noamkorinperi/VHDL_LAB_final/DOC/Final_report.pdf

## Final project – Report

## MCU and HW-Accelerators architecture and design

## נועם קורין פרי – 208138586

## רועי אגושביץ - 322720665

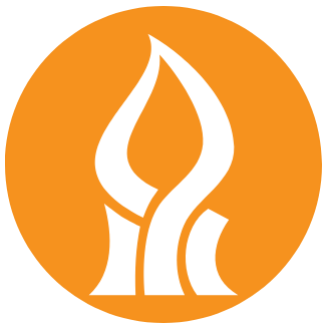
[picture p1: figure]

## תוכן עניינים

.1 הקדמה — עמוד 2
.2 הסבר על המערכת — עמוד 3 .3 תיאור קבצי ה־HDL — עמוד 4 .4 תצוגות RTL של המערכת — עמוד 8 .5 אימות פונקציונלי באמצעות ModelSim — עמוד 12
12 | עמוד | — Test1 – Pushbutton Interrupts and Divider 5.1
13 | עמוד | — Test2 – Basic Timer Periodic Interrupt 5.2
13 | עמוד | — Test3 – Reprogramming the Basic Timer 5.3
14 | עמוד | — Test4 – PWM / Output Compare 5.4
15 | עמוד | — Test4 – Input Capture and Divider 5.5
.6 אימות חומרתי באמצעות SignalTap — עמוד 16
16 | עמוד | — Test1 – KEY1 Interrupt 6.1
17 | עמוד | — Test2 – Basic Timer Interrupt 6.2
17 | עמוד | — Test3 – Basic Timer Interrupt 6.3
18 | עמוד | — Test4 – Integrated Hardware Validation 6.4
18 | עמוד | — Basic Timer Interrupt and CPU Response 6.4.1
18 | עמוד | — KEY1 Interrupt 6.4.2
19 | עמוד | — Divider Accelerator 6.4.3
20 | עמוד | — PWM – Output Compare 6.4.4
.7 אפיון ה־PPA של המערכת — עמוד 22 7.1 Area – ניצול משאבי FPGA — עמוד 22 7.2 Performance – תדר מקסימלי והנתיב הקריטי — עמוד 24 7.3 Power – צריכת הספק — עמוד 27 .8 מסקנות — עמוד 29

## .1 הקדמה

מטרת הפרויקט היא לתכנן ולממש מערכת MCU המבוססת על ליבת IM32RV בארכיטקטורת Cycle-Single, ולשלב סביבה מלאה הכוללת זיכרונות, רכיבי קלט/פלט, פסיקות ומאיץ חומרה. בדומה למעבד ממעבדה ,5 הליבה מבוססת על ארכיטקטורת Harvard ובה זיכרון פקודות ITCM וזיכרון נתונים DTCM, אך בפרויקט זה הורחבה המערכת כך שתתפקד כ־MCU מלא באמצעות O/I Mapped Memory ורכיבים פריפריאליים נוספים.

במסגרת הפרויקט מומשו ממשקי GPIO עבור הלדים, תצוגות ה־-7Segment והמתגים, ממשק ללחצנים 3KEY–1KEY עם תמיכה בפסיקות, Timer Basic הכולל ,Mode Compare
על | האחראי | Interrupt Controller וכן ,Input Captureו־ PWM | ליצירת | Output Compare
זיהוי מקור הפסיקה, קביעת עדיפויות והעברת ערך ה־TYPE למעבד. בנוסף שולב מאיץ חלוקה רב־מחזורי עבור פקודות DIV ו־REM, הפועל בדומיין שעון מהיר יותר ודורש מנגנון סנכרון בין תחומי השעון.

תהליך העבודה כלל כתיבת קוד VHDL ואינטגרציה של כלל רכיבי המערכת, אימות פונקציונלי ב־ModelSim באמצעות אפליקציות ה־Benchmark, אימות על גבי כרטיס ה־FPGA באמצעות SignalTap, ולבסוף אפיון PPA של המערכת ב־Quartus מבחינת שטח, ביצועים וצריכת הספק.

## .2 הסבר על המערכת

המערכת שתוכננה בפרויקט היא MCU המבוסס על ליבת Cycle-Single IM32RV. הליבה מחוברת לשני זיכרונות נפרדים בהתאם לארכיטקטורת Harvard: זיכרון ITCM עבור קוד התוכנית וזיכרון DTCM עבור נתונים. בנוסף לזיכרונות, המעבד מחובר למרחב כתובות של רכיבי O/I Mapped Memory, כך שפקודות load ו־store משמשות גם לגישה לרכיבים הפריפריאליים של המערכת. לפי חלוקת מרחב הכתובות, כתובות הזיכרון הנמוכות משמשות את ה־DTCM, בעוד הכתובות החל מ־2000x0 משמשות את רכיבי הקלט/פלט והבקרה.

רכיבי ה־GPIO כוללים ממשקים ל־LEDR, לתצוגות 5HEX–0HEX ולמתגים SW. עבור רכיבים בעלי יכולת פסיקה נוספו ממשק ללחצנים 3KEY–1KEY, ה־Timer Basic ובקר הפסיקות. ה־Timer Basic כולל רגיסטרי בקרה והשוואה ומאפשר יצירת פסיקות מחזוריות, אות PWM ומדידת זמן באמצעות Capture Input. בקר הפסיקות אוסף את דגלי הפסיקה, בודק אילו מקורות מאופשרים, קובע את המקור בעל העדיפות הגבוהה ביותר ומייצר את ערך ה־TYPE המתאים לפי טבלת וקטורי הפסיקות.

בנוסף לרכיבים הפריפריאליים, משולב במערכת מאיץ חלוקה רב־מחזורי. המאיץ מבצע פעולות חלוקה ושארית במשך 32 מחזורי DIVCLK, בעוד המעבד עצמו פועל על MCLK. בזמן פעולת המאיץ המעבד ממתין לסיום החישוב, ולאחר מכן התוצאה מוחזרת לנתיב ה־Writeback. מכיוון שמדובר בשני תחומי שעון שונים, שולב גם מנגנון CDC לצורך סנכרון האותות ביניהם.

במימוש הסופי נעשה שימוש בשלושה שעונים: MCLK עבור המעבד, SMCLK עבור ה־Timer Basic ו־DIVCLK עבור מאיץ החלוקה. מבנה זה מאפשר להפעיל את המאיץ בתדר גבוה יותר מהליבה, תוך שמירה על פעולה מסודרת של שאר רכיבי ה־MCU.

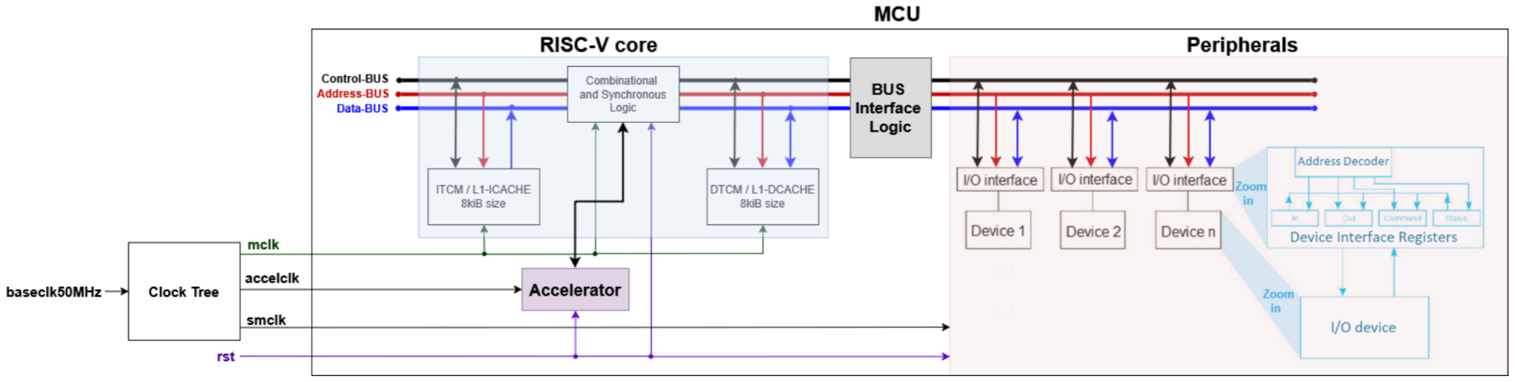
[picture p2: figure]

איור 1 – מבנה ה־Level Top של מערכת ה־MCU based-IM32RV.

## .3 תיאור קבצי ה־HDL

להלן תיאור קצר של קבצי ה־HDL המרכיבים את המימוש הסופי של ה־MCU. קבצי ה־DUT כוללים את ליבת ה־IM32RV, זיכרונות ויחידות הבקרה, רכיבי ה־MMIO, בקר הפסיקות, ה־Timer Basic ומאיץ החלוקה. רשימת הקבצים תואמת למימוש שנמצא .DUT/RV32IMscMCUב־

| קובץ תיאור
Structural בין ליבת המעבד, ה־DTCM, ה־Interconnect, הרכיבים הפריפריאליים ומערכת השעונים, ומחבר את כניסות ויציאות המערכת לכרטיס ה־FPGA. | vhd.IMscMCU32RV קובץ ה־Level Top של המערכת. מחבר באופן
.RV32IM Single-Cycleה־ ליבת של Top Levelה־ קובץ מחבר את יחידות ה־Control ,Decode ,Fetch ו־Execute, וכן את מאיץ ה־Divider ואת מנגנון הטיפול בפסיקות. | RV32I_CORE.vhd

מזיכרון ה־ITCM. בנוסף בוחר את כתובת הפקודה הבאה בהתאם לרצף רגיל, Branch או Jump. | VHD.IFETCH אחראי על ה־Counter Program ועל שליפת הפקודה
מה־File Register, כתיבה חזרה לרגיסטרים ויצירת ערכי ה־Immediate השונים. | VHD.IDECODE מבצע את שלב פענוח הפקודה, כולל קריאת האופרנדים
הפקודה ומייצרת את אותות הבקרה עבור ה־ALU, הזיכרון, Jump/Branch ופקודות ה־Extension M כגון .REMו־ MUL, DIV | VHD.CONTROL יחידת הבקרה הקומבינטורית של המעבד. מפענחת את
חישובי כתובות וזיהוי תנאי Branch. בנוסף משולב בו נתיב הביצוע עבור פעולות הכפל. | VHD.EXECUTE מבצע את הפעולות האריתמטיות והלוגיות של ה־ALU,
והכתיבה של המעבד. | VHD.DMEMORY מממש את זיכרון הנתונים DTCM, כולל פעולות הקריאה
הכפלת שני האופרנדים והפקת תוצאת הכפל לנתיב הביצוע. | vhd16.Multiplier מממש את יחידת הכפל של פקודת MUL, המבוססת על
המערכת משעון ה־50 MHz של הכרטיס. במימוש הסופי | vhd.PLL מממש את ה־PLL המשמש להפקת שעון העבודה של

ליבת המעבד פועלת ב־20 MHz, בעוד מאיץ החלוקה משתמש ב־50 MHz.

הטיימר תומך ב־Mode Compare ליצירת פסיקות Inputו־ PWM ליצירת Output Compare , מחזוריות Capture לשמירת ערך המונה בעת אירוע חיצוני. | vhd.timer_basic מממש את ה־Timer Basic ואת רגיסטרי הבקרה שלו.
רגיסטרי IE ו־IFG, קובע את מקור הפסיקה בעל העדיפות הגבוהה ביותר, מפיק את ערך ה־TYPE ומייצר את אות INTR למעבד. | vhd.controller_interrupt מממש את בקר הפסיקות של המערכת. שומר את
מצב הלחצנים ומייצר אירוע פסיקה בעת שחרור לחצן, בהתאם למעבר מ־0 ל־1 של אות ה־KEY. | vhd.unit_pushbutton מממש את ממשק 3KEY–1KEY. מאפשר קריאה של
תצוגות 5HEX–0HEX והמתגים SW, כולל קריאה וכתיבה לפי כתובות ה־MMIO. | vhd.peripheral_gpio מממש את רכיבי ה־GPIO הממופים לזיכרון: LEDR,
ומחבר ביניהם לבין ממשק ה־MMIO. כולל את ה־GPIO, הלחצנים, ה־Timer Basic ובקר הפסיקות. | vhd.peripherals_mcu מרכז את כלל הרכיבים הפריפריאליים של ה־MCU
שמפיק המעבד ומנתב כל פעולת Store/Load אל | vhd.interconnect_mcu מממש את לוגיקת ה־Interface Bus. בודק את הכתובת

ה־DTCM או אל מרחב ה־MMIO, ומחזיר למעבד את הנתונים מהיעד המתאים.

מכיל את קבועי מפת הזיכרון של ה־MCU, ובהם תחומי ה־DTCM וה־MMIO והכתובות של רכיבי ה־GPIO, הטיימר ובקר הפסיקות. | mcu_memory_map_pkg.vh d
החלוקה מתבצעת באלגוריתם רב־מחזורי במשך 32 מחזורי שעון ומפיקה מנה ושארית. | vhd.unsigned_divider מממש את ליבת המחלק הבלתי־מסומן. פעולת
מטפל בפקודות REM/DIV, באותות done/busy ובמעבר בין תחום שעון ה־MCLK לתחום ה־DIVCLK באמצעות מנגנון CDC. | vhd.accelerator_divider עוטף את המחלק ומחבר אותו לליבת המעבד. הקובץ
מסכות לפענוח פקודות וקבועים המשמשים את יחידות ה־Control וה־Datapath. | vhd.package_const מכיל קבועים משותפים לליבת המעבד, כגון Opcodes,
מכיל פרמטרים גלובליים של התכן, כגון גדלי הזיכרונות ורוחבי הכתובות, ומשמש להגדרת תצורת הקומפילציה של המערכת. | cond_compilation_package .vhd
משותפות Genericsו־ Components הצהרות מכיל המשמשות לחיבור מבני של יחידות המעבד והמערכת. | aux_package.vhd

## .4 תצוגות RTL של המערכת

לאחר השלמת הסינתזה ב־Quartus נבדק מבנה המערכת באמצעות ה־Viewer RTL. מטרת הבדיקה היא לוודא שהמודולים המרכזיים של המערכת חוברו כפי שתוכנן, ולראות את ההיררכיה והקשרים בין ליבת המעבד, הזיכרונות, הרכיבים הפריפריאליים ומאיץ החלוקה. דרישה להצגת תוצאות ה־Viewer RTL מופיעה במפורש בסעיף 10 של הוראות הפרויקט.

בתצוגת ה־Level Top ניתן לראות את ליבת ה־Cycle-Single IM32RV מחוברת ל־ITCM ול־DTCM, את ממשק ה־MMIO המחבר את המעבד לרכיבי ה־GPIO ולרכיבים בעלי יכולת פסיקה, וכן את מערכת השעונים והחיבור למאיץ החלוקה. המבנה משקף את ארכיטקטורת ה־MCU הכללית שנדרשה בפרויקט.

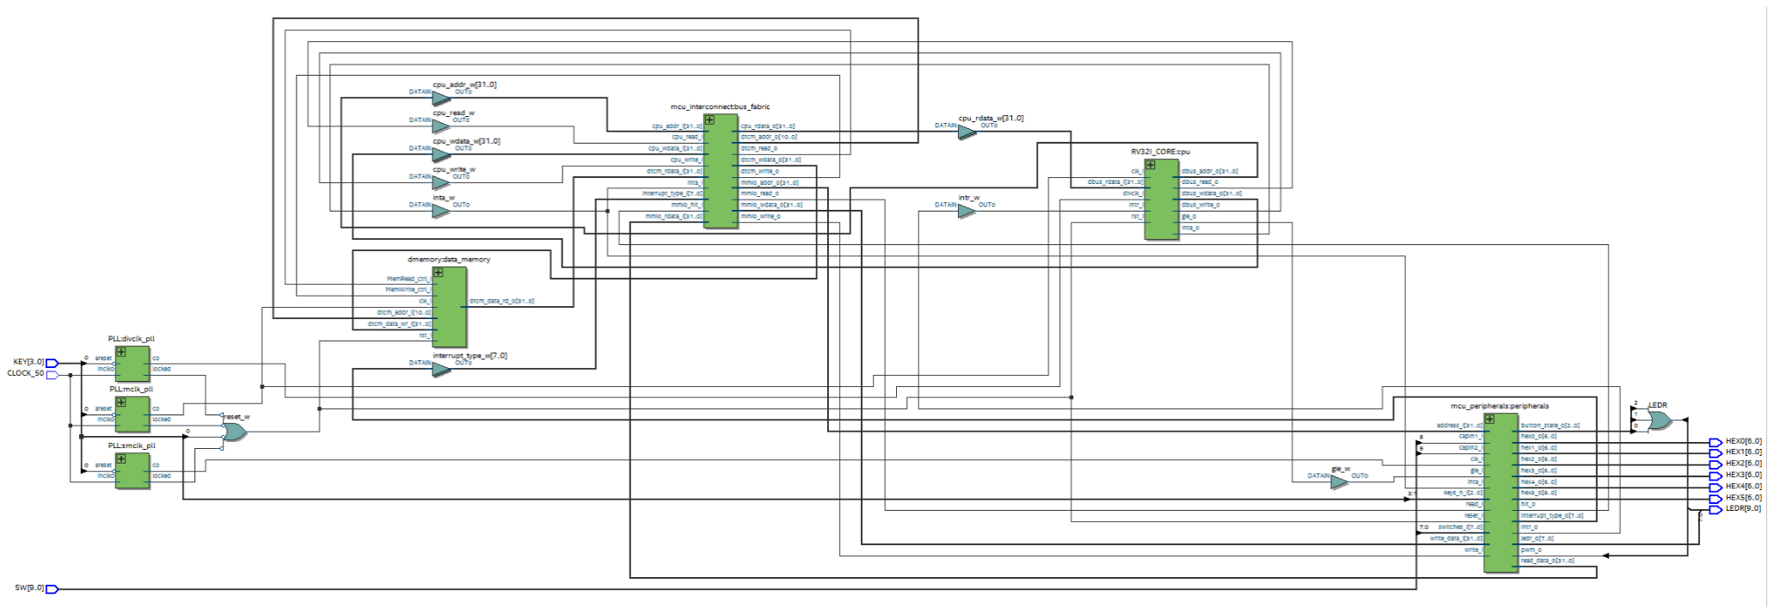
[picture p3: figure]

איור 2 - תצוגת RTL של ה־Level Top של מערכת ה־MCU based-IM32RV.

בנוסף נבדקה תצוגת ה־RTL של ליבת המעבד ושל נתיב מאיץ החלוקה. ניתן לראות את יחידות ה־Control ,Decode ,Fetch ו־Execute של הליבה החד־מחזורית, וכן את החיבור בין האופרנדים של המעבד למאיץ ה־Divider ואת החזרת תוצאת ה־Quotient או ה־Remainder לנתיב ה־Writeback. מבנה זה תואם לארכיטקטורה הנדרשת של ליבת IM32RV עם מאיץ חלוקה רב־מחזורי.

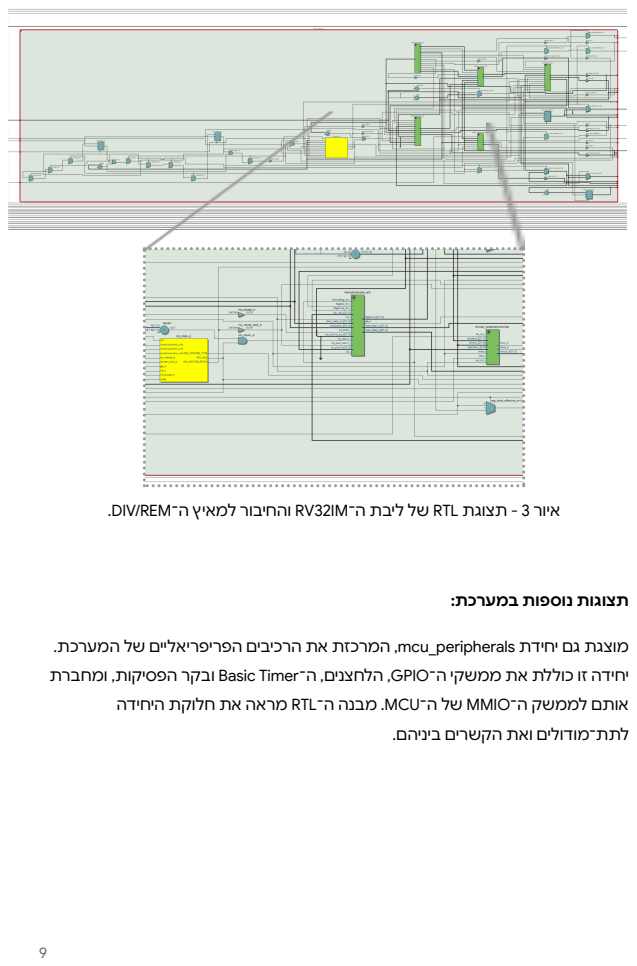
[picture p4: page 10]

איור 3 - תצוגת RTL של ליבת ה־IM32RV והחיבור למאיץ ה־REM/DIV.

תצוגות נוספות במערכת:

מוצגת גם יחידת peripherals_mcu, המרכזת את הרכיבים הפריפריאליים של המערכת.
יחידה זו כוללת את ממשקי ה־GPIO, הלחצנים, ה־Timer Basic ובקר הפסיקות, ומחברת

אותם לממשק ה־MMIO של ה־MCU. מבנה ה־RTL מראה את חלוקת היחידה

לתת־מודולים ואת הקשרים ביניהם.

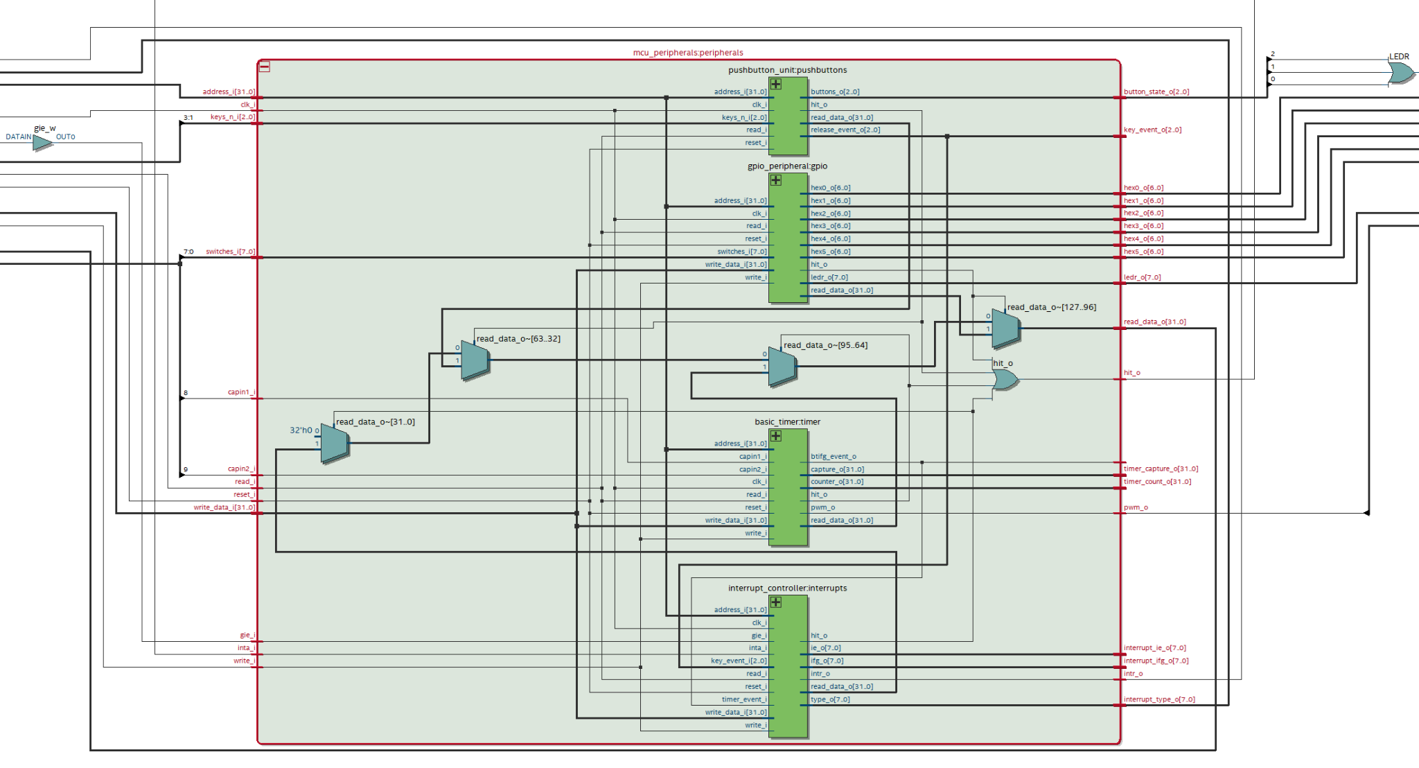
[picture p5: figure]

איור 4 – תצוגת RTL של מערך הרכיבים הפריפריאליים של ה־MCU.

בהמשך נבחן גם ה־Controller Interrupt, שהוא אחד הרכיבים המרכזיים שנוספו למערכת לצורך תמיכה בפסיקות. ניתן לזהות בו את הלוגיקה הקשורה לרגיסטרי IFG ,IE ו־TYPE, וכן את החיבור למקורות הפסיקה השונים. הבקר אחראי לסינון הפסיקות לפי ביטי ה־Enable, לקביעת מקור הפסיקה בעל העדיפות הגבוהה ביותר ולהעברת בקשת הפסיקה וה־TYPE המתאים אל המעבד.

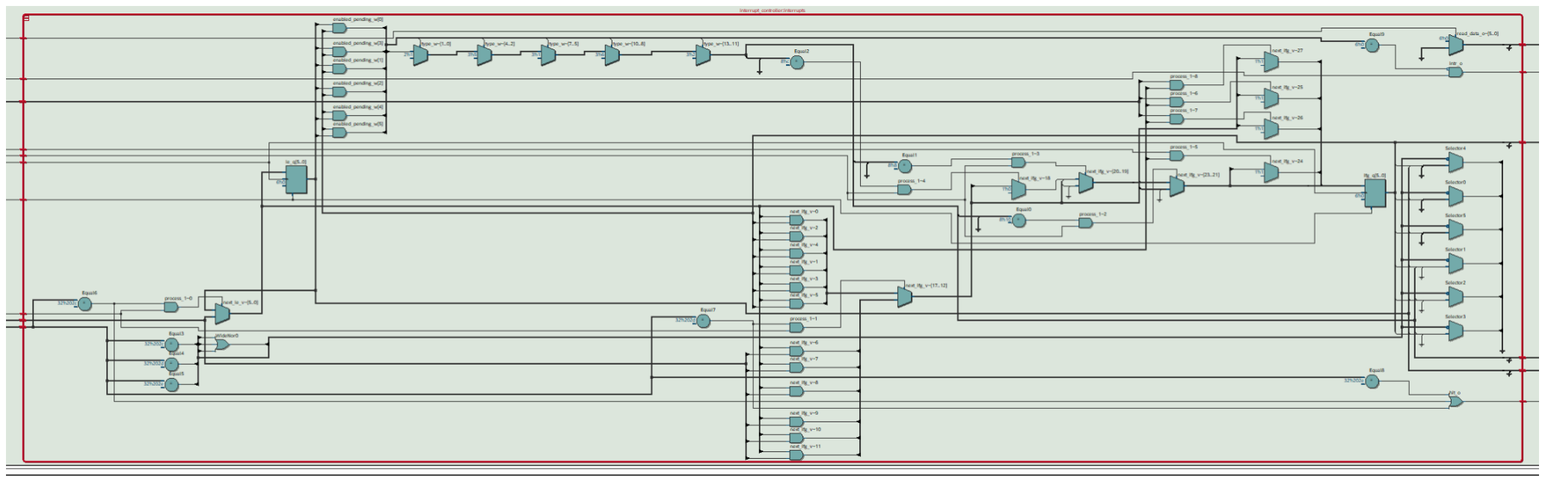
[picture p6: figure]

איור 5 – תצוגת RTL של בקר הפסיקות.

לבסוף נציג גם את מערכת השעונים של ה־MCU. המערכת משתמשת בשלושה אותות שעון נפרדים המופקים מ־50_CLOCK: MCLK עבור ליבת המעבד, SMCLK עבור ה־Basic Timer ו־DIVCLK עבור מאיץ החלוקה. במימוש הסופי MCLK ו־SMCLK פועלים בתדר 20 MHz, בעוד DIVCLK פועל בתדר 50 MHz.

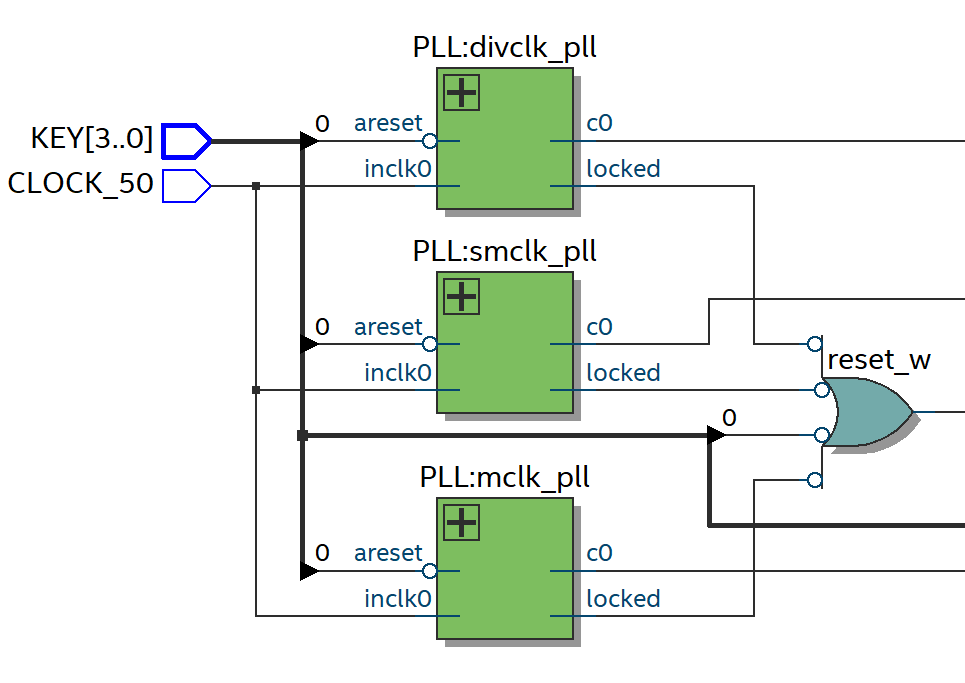
[picture p7: figure]

איור 6 – תצוגת RTL של מערכת השעונים וה־PLL של ה־MCU.

## .5 אימות פונקציונלי באמצעות ModelSim

לאחר השלמת האינטגרציה של רכיבי ה־MCU בוצע אימות פונקציונלי ב־ModelSim באמצעות ארבע אפליקציות ה־Benchmark שניתנו לפרויקט. מטרת הסימולציות הייתה לבדוק לא רק את פעולת כל רכיב בנפרד, אלא גם את שיתוף הפעולה בין ליבת המעבד, ה־O/I Mapped Memory, בקר הפסיקות, ה־Timer Basic ומאיץ החלוקה. במהלך ההרצות נבדקו אותות ה־MMIO, דגלי הפסיקה, אותות INTR ו־INTA, פעילות ה־Divider וכן רגיסטרי ה־Timer Basic.

Test1 – Pushbutton Interrupts and Divider 5.1

ב־1Test נבדקה תגובת המערכת לפסיקות הנוצרות מהלחצנים 3KEY–1KEY. לחיצות 1KEY ו־2KEY משמשות להצגת איברים מהמערכים על תצוגות ה־HEX, ואילו 3KEY מפעיל פעולות DIV ו־REM באמצעות מאיץ החלוקה. בתרשים הגלים ניתן לעקוב אחר שרשרת הטיפול בפסיקה החל משינוי מצב ה־KEY, דרך יצירת דגל ה־IFG והעלאת INTR, ועד לאישור הפסיקה על ידי המעבד באמצעות INTA. בהמשך ניתן לראות גם את פעילות מאיץ ה־Divider ואת החזרת תוצאת החישוב למעבד. לדוגמה, עבור האופרנדים הראשונים 100=1arr ו־8=2arr מתקבלים מנה 12 ושארית ,4 בהתאם לתוצאה הצפויה.

המטרה של הבדיקה היא להראות שמסלול הפסיקה מהלחצן אל המעבד פועל כראוי, ושלאחר הטיפול בפסיקה המעבד מסוגל להפעיל את מאיץ החלוקה ולקבל ממנו תוצאה תקינה.

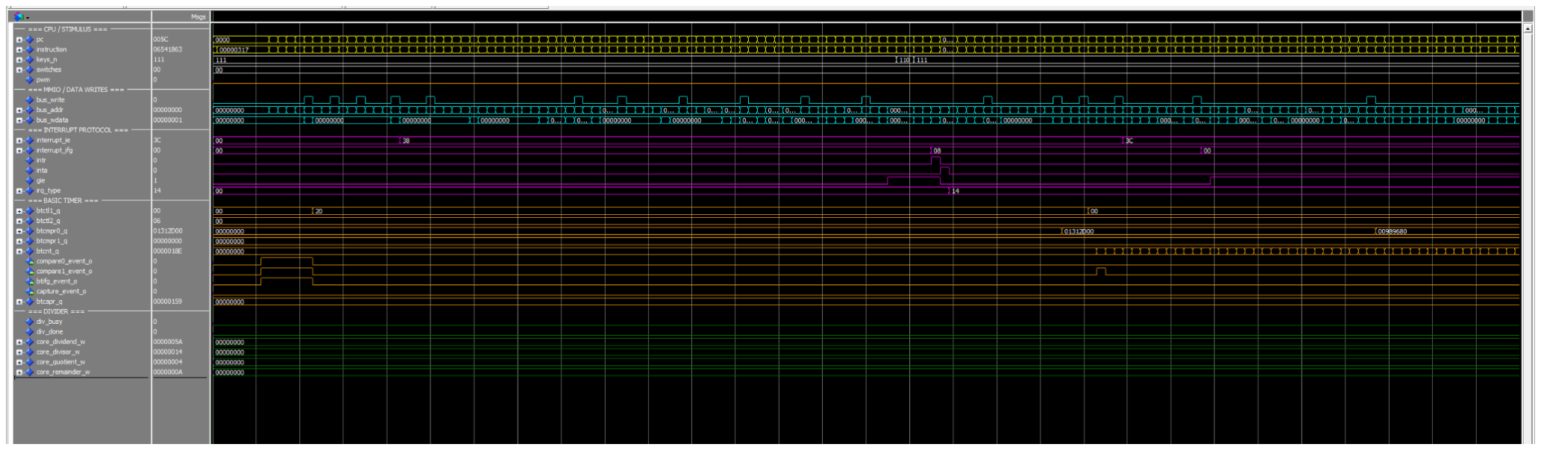
[picture p8: figure]

איור 7 – סימולציית ModelSim של 1Test – פסיקות לחצנים ופעולת מאיץ ה־Divider.

Test2 – Basic Timer Periodic Interrupt 5.2

ב־2Test נבדקה פעולת ה־Timer Basic כמקור לפסיקה מחזורית. בכל אירוע Timer נוצר BTIFG, בקר הפסיקות מזהה את מקור הפסיקה ומעביר למעבד 10x0=TYPE, בהתאם לטבלת וקטורי הפסיקות. לאחר מכן המעבד מאשר את הפסיקה באמצעות INTA ונכנס לשגרת הטיפול המתאימה.

שגרת הפסיקה מגדילה את הרגיסטר 0a, כאשר 3KEY–1KEY קובעים באיזה זוג תצוגות HEX יוצג הערך. בתרשים הגלים ניתן לראות את אירוע הטיימר, עדכון ה־IFG, יצירת INTR, אישור הפסיקה ולבסוף את עדכון הערך. לאחר הפסיקה הראשונה מתקבל 1=0a, כפי שנדרש באפליקציית ה־Benchmark. בדיקה זו מאמתת את שרשרת הטיפול המלאה בפסיקה פנימית של ה־MCU, החל מה־Timer Basic ועד לביצוע שגרת הפסיקה על ידי המעבד.

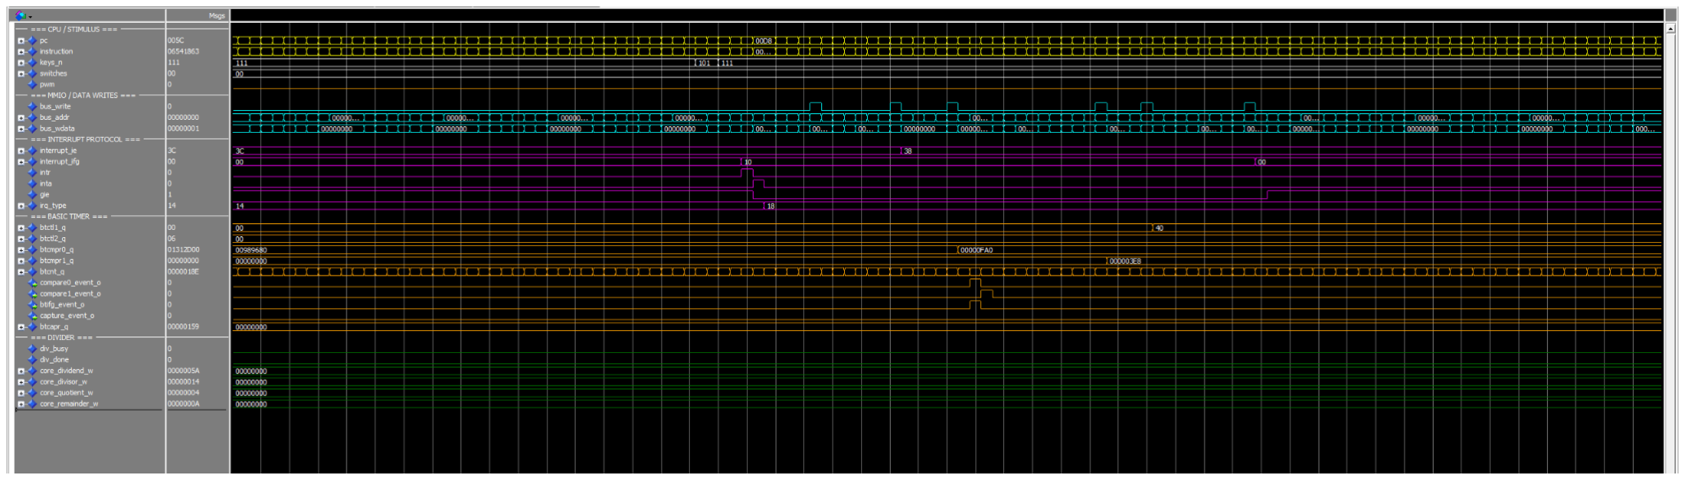
[picture p9: figure]

איור 8 – סימולציית ModelSim של 2Test – פסיקה מחזורית של ה־Timer Basic.

Test3 – Reprogramming the Basic Timer 5.3

ב־3Test נבדקה האפשרות לשנות בזמן ריצה את תקופת הפסיקות של ה־Timer Basic. לחיצות על 2KEY 1,KEY ו־3KEY גורמות לכתיבת ערכים חדשים ל־0BTCMPR, המתאימים לתקופות של /2PERIOD_SEC, /4PERIOD_SEC ו־/8PERIOD_SEC. בתרשים הגלים ניתן לראות את כתיבות ה־MMIO לרגיסטר ההשוואה ואת השינוי בהתנהגות הטיימר לאחר התכנות מחדש. בנוסף נבדקה פעולת מנגנון ה־buffering double של רגיסטר ההשוואה: הערך החדש נכתב ל־0BTCMPR ומועבר ל־Latch המשמש בפועל להשוואה מול BTCNT,

כך ששינוי ערך ההשוואה מתבצע בצורה מבוקרת. מנגנון זה תואם למבנה ה־Timer Basic שהוגדר בפרויקט.

הבדיקה מראה כי תוכנת ה־Benchmark מסוגלת לשנות את תקופת הטיימר בזמן ריצה באמצעות כתיבות MMIO, וכי הפסיקות הבאות מתקבלות בהתאם לערך ההשוואה החדש.

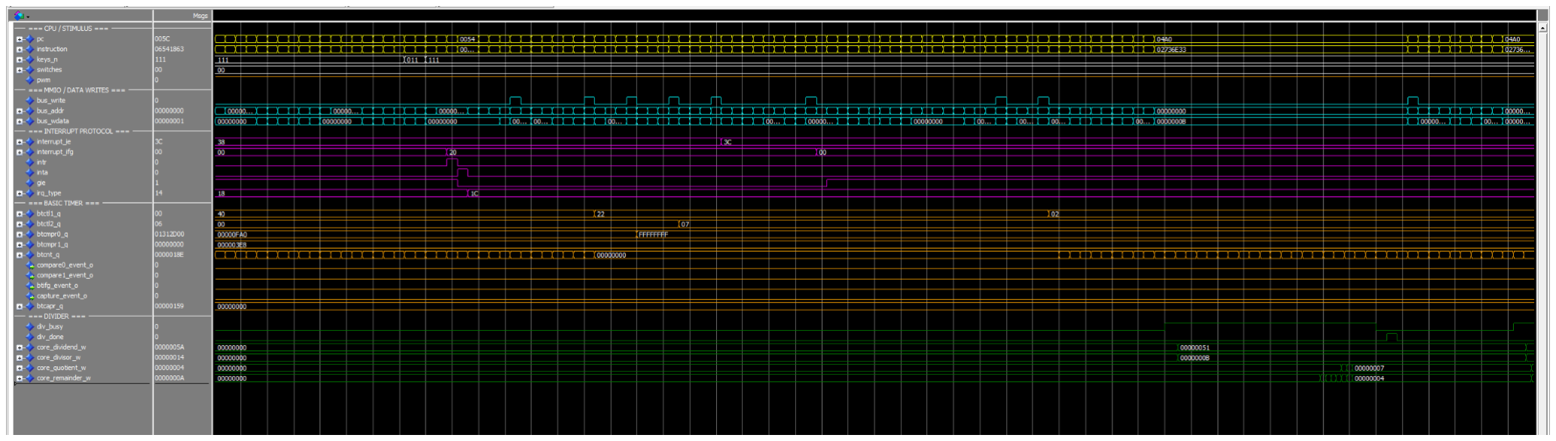
[picture p10: figure]

איור 9 – סימולציית ModelSim של 3Test – תכנות מחדש של תקופת ה־Timer Basic.

Test4 – PWM / Output Compare 5.4

החלק הראשון של 4Test בודק את מצב ה־Compare Output של ה־Timer Basic ואת יצירת אות ה־PWM. לאחר לחיצה על 2KEY מבוצעות כתיבות MMIO לרגיסטרי הטיימר, ובפרט ל־0BTCMPR ול־1BTCMPR.

0BTCMPR קובע את תקופת ה־PWM ונשאר בערך 0FA00000x0( 4000 מחזורי SMCLK), בעוד 1BTCMPR קובע את נקודת ההשוואה בתוך המחזור. ה־Benchmark משנה את ערך 1BTCMPR כך שמתקבלים Cycles Duty של ,50% ,75% 87.5% ו־.93.75% בתרשים ModelSim ניתן לראות את כתיבות ה־MMIO ואת שינוי ערכי רגיסטרי ההשוואה; ההתנהגות הפיזית של אות ה־PWM עצמו נבדקת בהמשך באמצעות SignalTap.

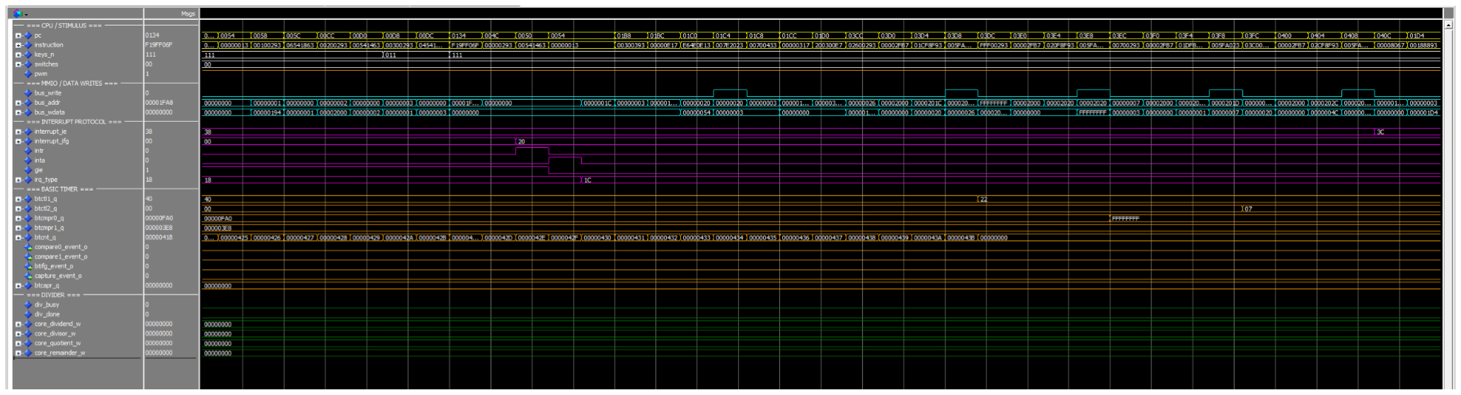
[picture p11: figure]

איור 10 – סימולציית ModelSim של 4Test – תכנות ה־Timer Basic במצב Output .Compare / PWM

Test4 – Input Capture and Divider 5.5

בחלק נוסף של 4Test נבדק מצב ה־Capture Input של ה־Timer Basic, המשמש למדידת זמן הריצה של פעולות DIV ו־REM. מאיץ החלוקה פועל במשך מספר מחזורי DIVCLK, ובסיום הפעולה מופק אירוע המשמש ללכידת ערך BTCNT לתוך BTCAPR.

בתרשים ניתן לראות את אותות ה־done/busy של מאיץ החלוקה, את האופרנדים והתוצאות, ובמקביל את אירוע ה־Capture ואת עדכון BTCAPR. אפליקציית ה־Benchmark מבצעת סדרת פעולות REM ולאחר מכן DIV, וה־Testbench מאמת שתוצאות המערכים נשמרו ושערכי זמן הריצה שנלכדו אינם אפס. בדיקה זו מאמתת את העבודה המשותפת בין שלושה חלקים מרכזיים במערכת: ליבת המעבד, מאיץ ה־Divider .Basic Timerוה־

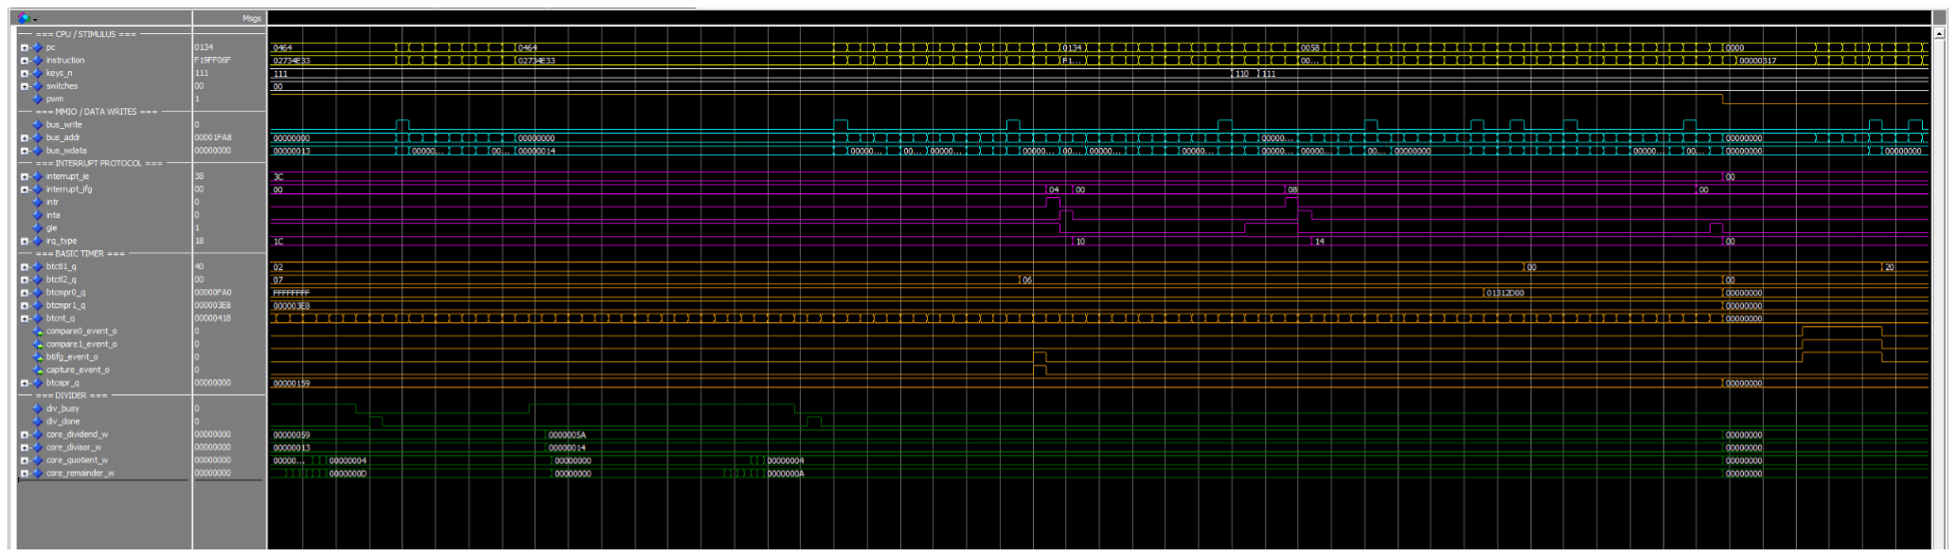
[picture p12: figure]

איור 11 – סימולציית ModelSim של Capture Input – 4Test ומדידת פעולת ה־Divider.

ארבע בדיקות ה־Benchmark מאפשרות לבדוק את המערכת ברמת אינטגרציה מלאה ולא רק ברמת יחידות בודדות. הסימולציות מאמתות את פעולת ה־GPIO והלחצנים,
,Input Captureו־ Compare, Output Compare | במצבי | Basic Timerה־ , | הפסיקות | מנגנון
וכן את פעולת מאיץ ה־REM/DIV והתקשורת שלו עם ליבת המעבד.

## .6 אימות חומרתי באמצעות SignalTap

לאחר השלמת האימות הפונקציונלי ב־ModelSim, בוצע אימות של המערכת על גבי כרטיס ה־FPGA באמצעות SignalTap. מטרת הבדיקה הייתה לוודא שהתנהגות המערכת שנצפתה בסימולציה מתקיימת גם במימוש הפיזי לאחר סינתזה ו־Route & Place. במהלך הרצת אפליקציות ה־Benchmark נלכדו אותות פנימיים מרכזיים, ובהם רגיסטר ה־IFG,
רגיסטרי | ,PCה־ | רצף ,irq_vector_load_wו־ irq_accept_w ,INTA | אותות | ,TYPEה־ | ערך
ה־Timer Basic ואותות מאיץ החלוקה.

Test1 – KEY1 Interrupt 6.1

במהלך הרצת 1Test נלכד ב־SignalTap תהליך הטיפול בפסיקת 1KEY. באיור 12 ניתן לראות כי רגיסטר ה־IFG מקבל את הערך h,08 המתאים ל־IFG1KEY, ובמקביל w_type_interrupt מקבל את הערך h,14 בהתאם לטבלת וקטורי הפסיקות. לאחר מכן הערך h14 נלכד ב־q_type_irq.

ובמקביל | ,irq_vector_load_wו־ INTA ,irq_accept_w | מופעלים | הלכידה | בהמשך
משתנה רצף ה־PC. בכך מאומת בחומרה מסלול הטיפול בפסיקת 1KEY, החל מזיהוי מקור הפסיקה ועד להעברת המעבד לשגרת הפסיקה.

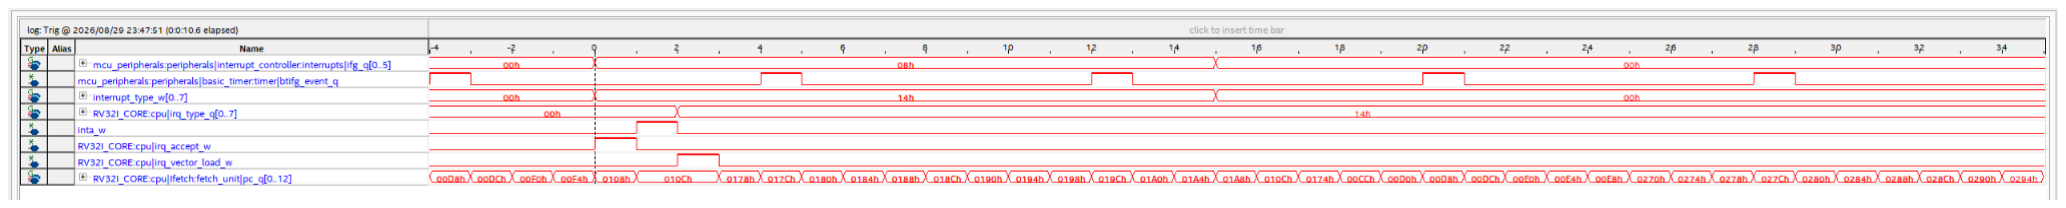
[picture p13: figure]

איור 12 – אימות SignalTap של 1Test – טיפול בפסיקת 1KEY.

Test2 – Basic Timer Interrupt 6.2

ב־2Test נלכדה פסיקה שמקורה ב־Timer Basic. באיור 13 ניתן לראות את עליית q_event_btifg, ולאחריה רגיסטר ה־IFG מקבל את הערך h,04 המתאים ל־BTIFG. במקביל בקר הפסיקות מפיק h10=TYPE, והערך נלכד ב־q_type_irq.

ורצף | ,irq_vector_load_wו־ INTA ,irq_accept_w | מופעלים | הפסיקה | זיהוי | לאחר
ה־PC משתנה בהתאם לכניסה לשגרת הטיפול בפסיקה. הלכידה מאמתת את שרשרת הטיפול המלאה בפסיקת Timer Basic על גבי ה־FPGA.

איור 13 – אימות SignalTap של 2Test – טיפול בפסיקת Timer Basic.

Test3 – Basic Timer Interrupt 6.3

במהלך 3Test נלכדה שוב פסיקה שמקורה ב־Timer Basic. באיור 14 ניתן לראות את q_event_btifg, את עדכון ה־IFG ל־h04 ואת יצירת h10=TYPE. לאחר מכן מופעלים
עובר | PCוה־ ,irq_vector_load_wו־ INTA ,irq_accept_w | בפסיקה | הטיפול | אותות
לרצף המתאים לשגרת הפסיקה.

לכידה זו מאמתת כי גם במהלך 3Test מנגנון הפסיקות של ה־Timer Basic ממשיך לפעול באופן תקין לאחר תכנות הטיימר על ידי התוכנה.

איור 14 – אימות SignalTap של 3Test – טיפול בפסיקת Timer Basic.

Test4 – Integrated Hardware Validation 6.4

ב־4Test בוצע אימות חומרתי מפורט יותר של מספר מנגנונים במערכת: פסיקת Basic Timer ותגובת המעבד, פסיקת 1KEY, פעולת מאיץ החלוקה ויצירת אות PWM באמצעות .Output Compare

Basic Timer Interrupt and CPU Response 6.4.1

באיור 15 ניתן לראות את BTCNT מתקדם עד לערך ההשוואה 00989680x0=0BTCMPR. עם הגעת המונה לערך ההשוואה נוצר אירוע q_event_btifg, רגיסטר ה־IFG מתעדכן ל־h04 ובקר הפסיקות מפיק h10=TYPE. לאחר מכן הערך h10 נלכד ב־q_type_irq,
.irq_vector_load_wו־ INTA ,irq_accept_w | ומופעלים

באותה לכידה ניתן לראות גם את שינוי רצף ה־PC ואת חזרת BTCNT לערך אפס לאחר אירוע ההשוואה. בכך מאומת בחומרה הקשר המלא בין פעולת הטיימר לבין מנגנון הפסיקות ותגובת ה־CPU.

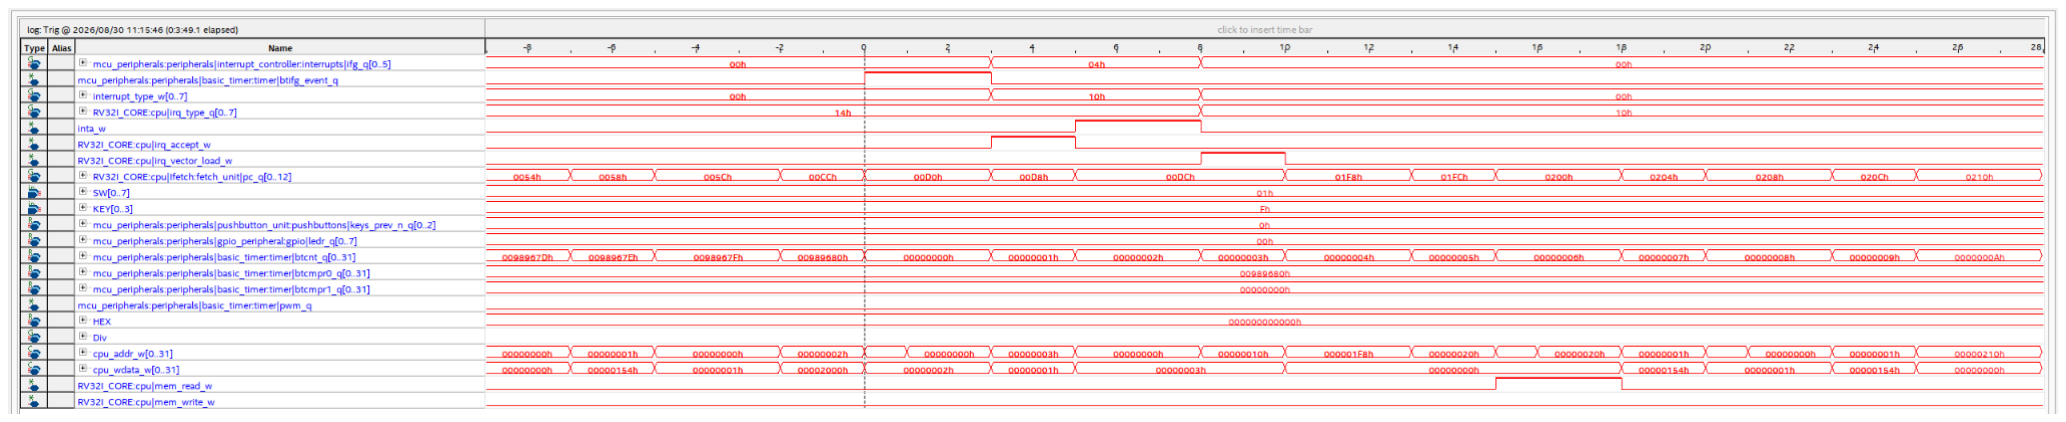
[picture p14: figure]

איור 15 – אימות SignalTap של 4Test – פסיקת Timer Basic ותגובת ה־CPU.

KEY1 Interrupt 6.4.2

באיור 16 מוצגת פסיקת 1KEY במהלך 4Test. ניתן לראות את אוטובוס 3:0]KEY ]משתנה מ־Dh ל־Fh, כלומר 1KEY עובר ממצב לחוץ למצב משוחרר. לאחר האירוע רגיסטר ה־IFG מקבל את הערך h,08 ו־w_type_interrupt מקבל h.14

INTA ,irq_accept_w | ומופעלים | ,irq_type_qב־ | נלכד | TYPE=14h | בהמשך
ו־w_load_vector_irq. במקביל משתנה ה־PC לשגרת הפסיקה. הלכידה מאמתת בחומרה את זיהוי אירוע 1KEY ואת הטיפול בו על ידי בקר הפסיקות והמעבד.

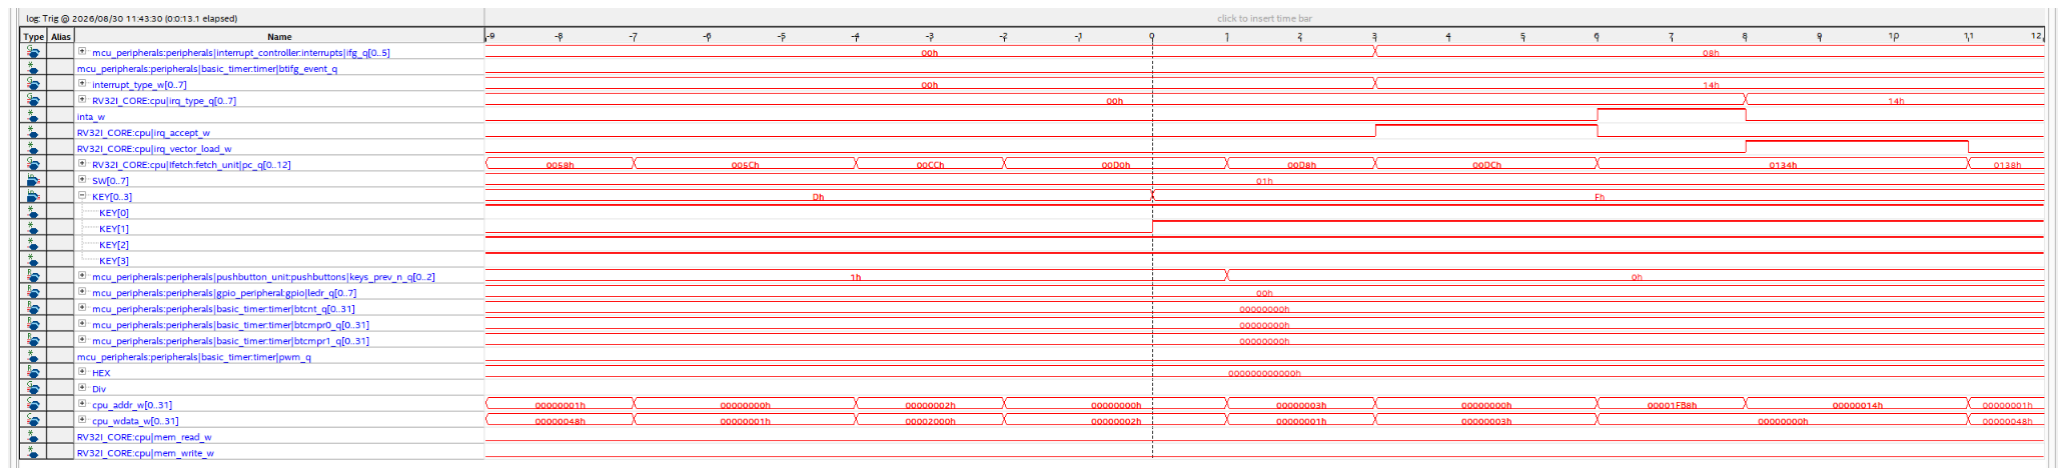
[picture p15: figure]

איור 16 – אימות SignalTap של 4Test – פסיקת 1KEY.

Divider Accelerator 6.4.3

באיור 17 מוצגת פעולת מאיץ החלוקה במהלך 4Test. ניתן לראות את התקדמות q_count עד Fh,1 ובמקביל את השינוי ההדרגתי ברגיסטרים הפנימיים של אלגוריתם החלוקה. האופרנד q_divisor שווה ל־,8 ובסיום הפעולה מתקבלים 7=q_quotient .remainder_q=4ו־

בסיום החישוב מופעל q_done, ולאחר מכן מתקבל גם w_done_div בצד המעבד. הלכידה מאמתת הן את פעולת האלגוריתם הרב־מחזורי לאורך מחזורי DIVCLK והן את העברת סימון סיום החישוב והתוצאה חזרה לליבת המעבד.

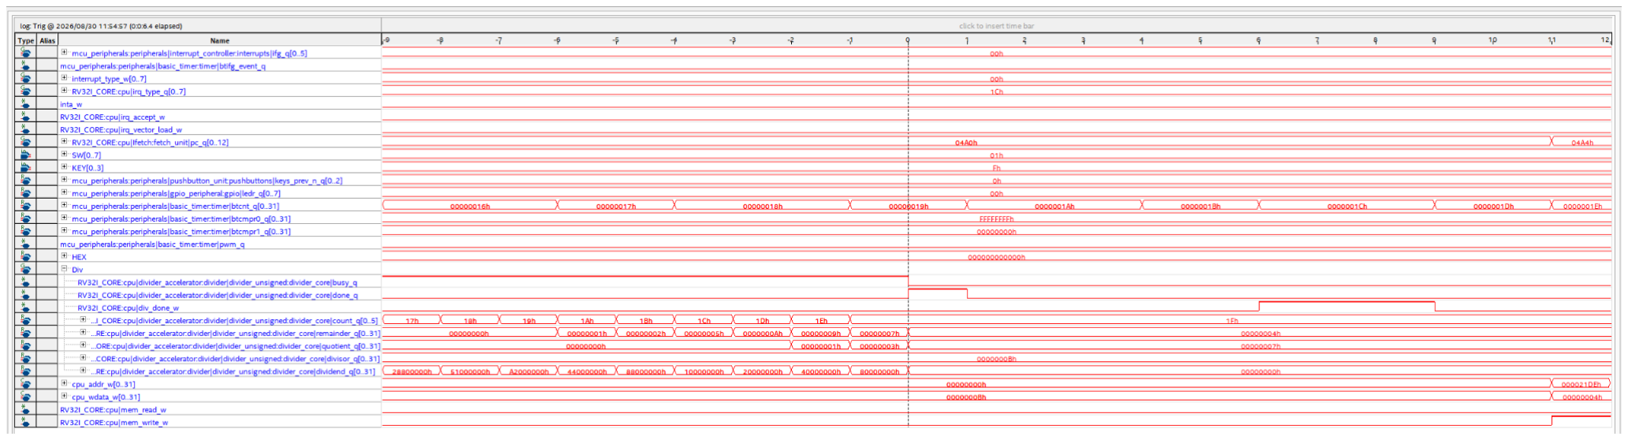
[picture p16: figure]

איור 17 – אימות SignalTap של 4Test – פעולת מאיץ ה־Divider.

PWM – Output Compare 6.4.4

בחלק האחרון של 4Test נבדקה פעולת ה־PWM של ה־Timer Basic. בכל ארבע הלכידות 0BTCMPR נשאר קבוע בערך 0FA00000x,0 כלומר 4000 מחזורי SMCLK, בעוד 1BTCMPR משתנה וקובע את נקודת ה־Compare Output.

באיורים 18–21 מתקבלים הערכים:

עבור | 0x00000DAC ,75% | עבור | 0x00000BB8 ,50% | עבור | BTCMPR1=0x000007D0
87.5% ו־6EA00000x0 עבור .93.75% ערכים אלו הם בהתאמה ,2000 ,3000 3500 ו־3750 מתוך תקופה של 4000 ספירות. במקביל מוצג האות pwm_q, ונקודת שינוי המצב שלו משתנה בהתאם לערך ההשוואה שנבחר.

כך מאומת כי שינוי 1BTCMPR באמצעות 4Test משנה בפועל את ה־Cycle Duty של אות ה־PWM, בעוד תקופת ה־PWM נשארת קבועה. עבור MHz 20=SMCLK ותקופה של 4000 מחזורים מתקבל תדר PWM של 5 kHz.

PWM Duty Cycle variation using KEY2

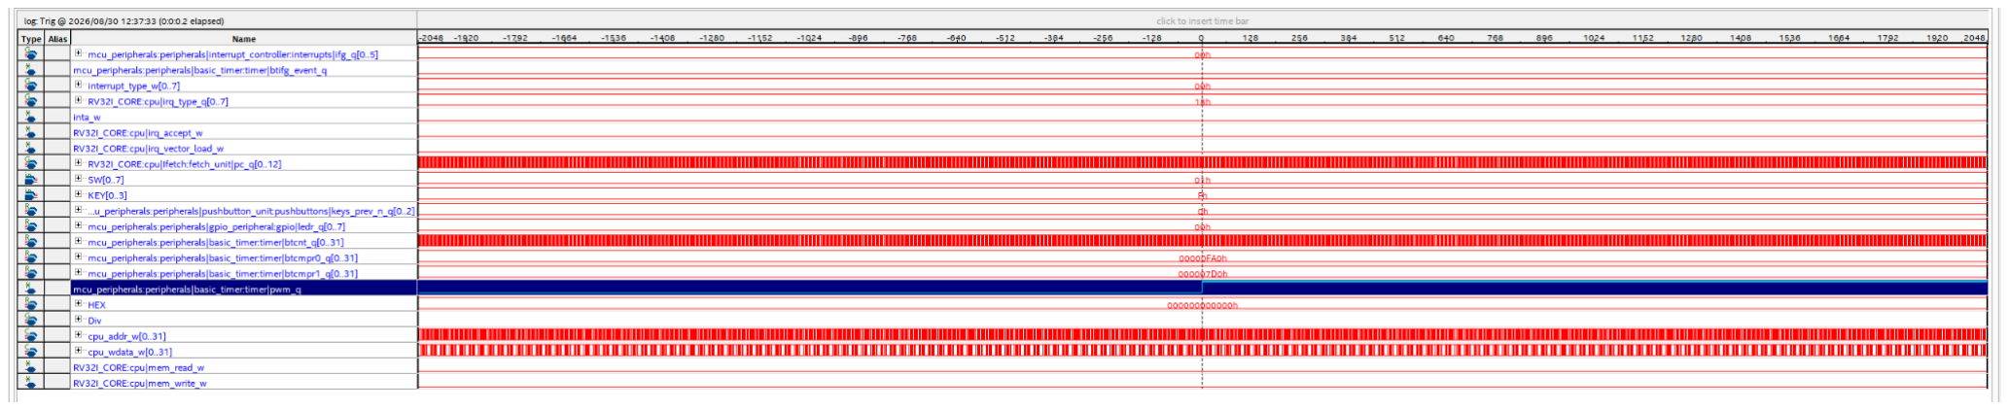
[picture p17: figure]

.BTCMPR1=0x000007D0 ,50% של Duty Cycleב־ PWM של SignalTap | אימות | – 18 איור

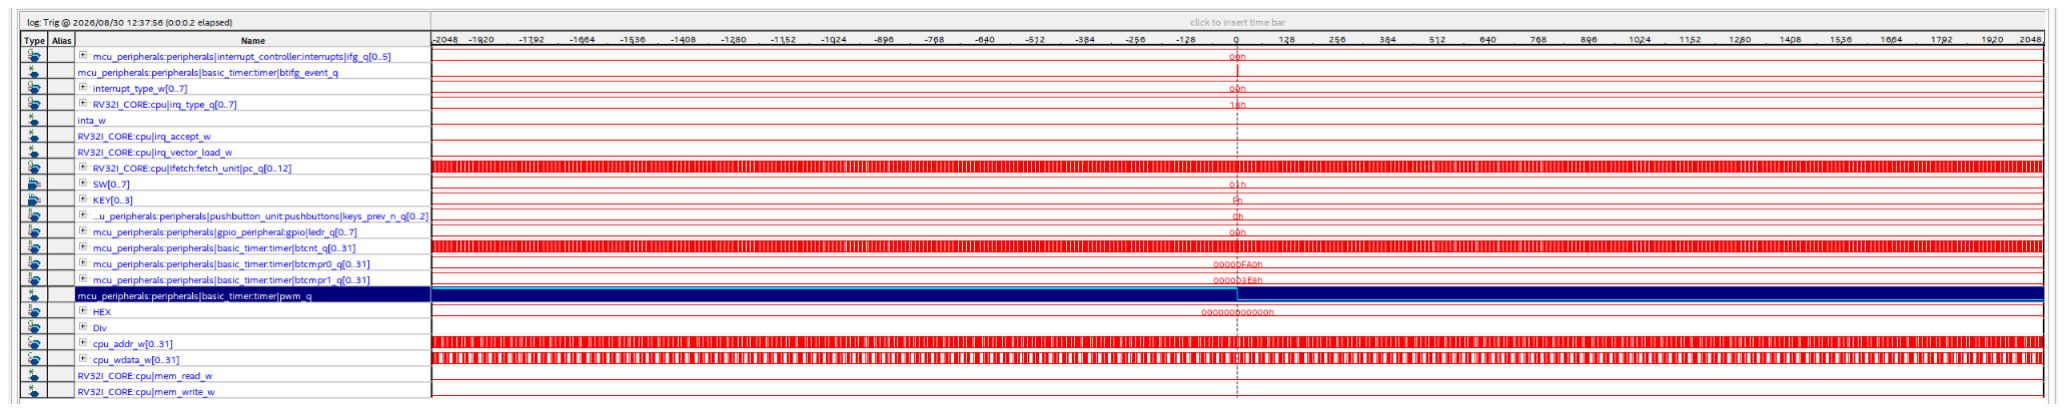
[picture p18: figure]

.BTCMPR1=0x00000BB8 ,75% של Duty Cycleב־ PWM של SignalTap | אימות | – 19 איור

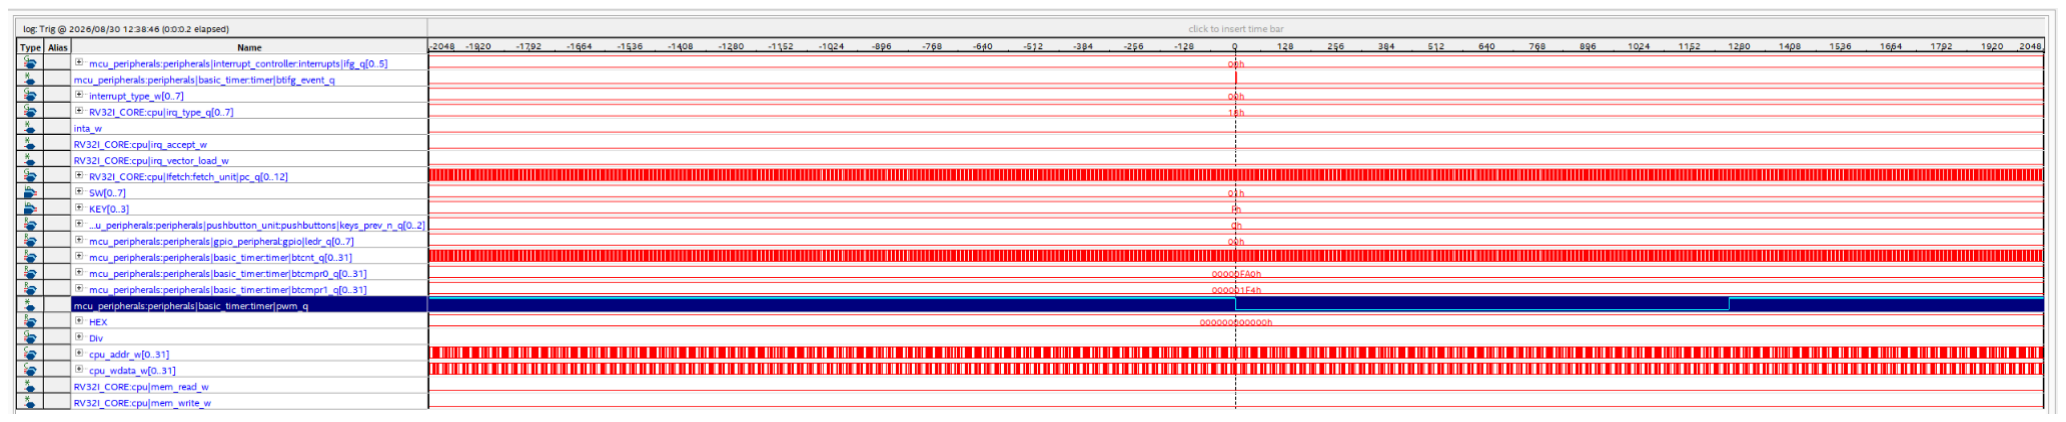
[picture p19: figure]

איור 20 – אימות SignalTap של PWM ב־Cycle Duty של ,87.5% .BTCMPR1=0x00000DAC

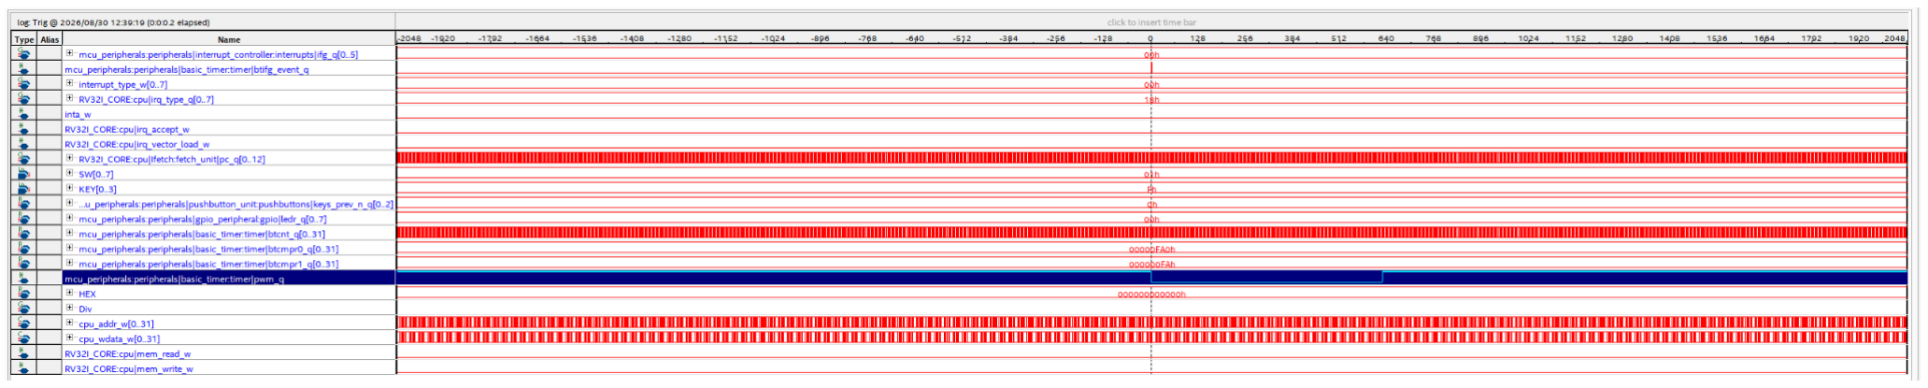
[picture p20: figure]

איור 21 – אימות SignalTap של PWM ב־Cycle Duty של ,93.75% .BTCMPR1=0x00000EA6

האימות באמצעות SignalTap הראה כי המנגנונים המרכזיים שנבדקו ב־ModelSim פועלים גם במימוש הפיזי על גבי ה־FPGA. נצפו בפועל מסלולי הטיפול בפסיקות של 1KEY ושל ה־Timer Basic, פעולת מאיץ החלוקה הרב־מחזורי ויצירת PWM עם ארבעה ערכי Cycle Duty שונים. בכך התקבל אימות חומרתי של האינטגרציה בין ליבת המעבד, בקר הפסיקות, ה־Timer Basic ומאיץ החלוקה.

## .7 אפיון ה-PPA( ביצועים, הספק, שטח( של המערכת:

לאחר השלמת האימות הפונקציונלי והחומרתי בוצע אפיון PPA ב־Quartus עבור שתי תצורות של המערכת: MCU הכולל רכיבי GPIO בלבד, ו־MCU מלא הכולל גם את הרכיבים בעלי יכולת הפסיקה. האפיון כולל את ניצול משאבי ה־FPGA, תדר העבודה המקסימלי והנתיב הקריטי, וכן את צריכת ההספק של שתי התצורות. בהתאם לדרישות הפרויקט, עבור כל אחד מהמדדים מצורפים גם דוחות ה־Quartus המתאימים.

### 7.1 Area - ניצול משאבי FPGA

תוצאות ה־Area מראות כי גרסת ה־GPIO בלבד משתמשת ב־1793 Elements Logic וב־1767 רגיסטרים, בעוד המימוש המלא משתמש ב־2074 Elements Logic וב־2007 רגיסטרים. כלומר, הוספת הרכיבים בעלי יכולת הפסיקה הגדילה את השימוש בלוגיקה ב־281 אלמנטים ואת מספר הרגיסטרים ב־.240

לעומת זאת, מספר פיני ה־O/I נשאר 67 בשתי התצורות, כמות הזיכרון המשובץ נשארה 131,072 ביטים, ומספר המכפלים וה־PLL נשאר ללא שינוי. בשני המימושים Quartus משתמש בארבעה בלוקי DSP עבור ארבעת המכפלים מסוג Unsigned Point Fixed Multiplier. מכאן ניתן לראות שהרחבת המערכת מתבטאת בעיקר בתוספת לוגיקה ורשמים עבור הרכיבים הפריפריאליים ומנגנון הפסיקות.

Area

| Logic elements | Registers | I/O pins | Embedde d memory bits | Embedded 9-bit Multipliers | PLLs
MCU with GPIO | 1793 | 1767 | 67 | 131,072 | 4 | 1
MCU with GPIO and Interrupt Capability | 2074 | 2007 | 67 | 131,072 | 4 | 1

________________________________ MCU with GPIO:

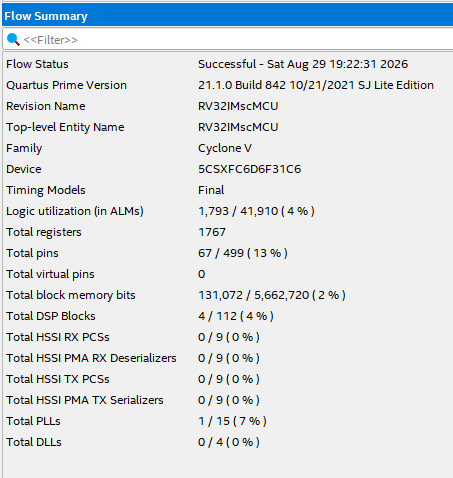
[picture p21: figure]

________________________________
MCU with GPIO and Interrupt Capability:

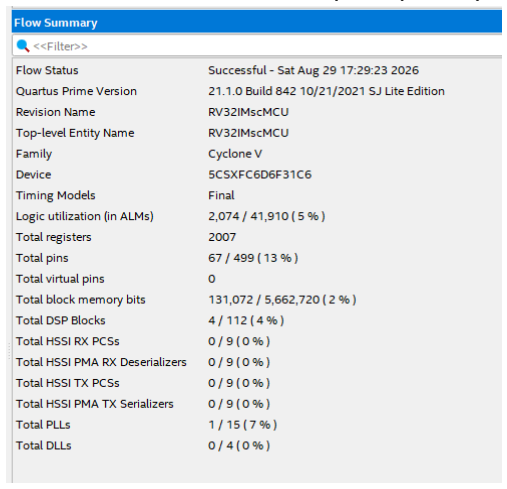
[picture p22: figure]

________________________________ בנוסף ניתן לראות כי שני המימושים משתמש ב־4 מכפלים מסוג Unsigned Point Fixed
.DSP blocks 4 | באמצעות | הממומשים | ,Multiplier

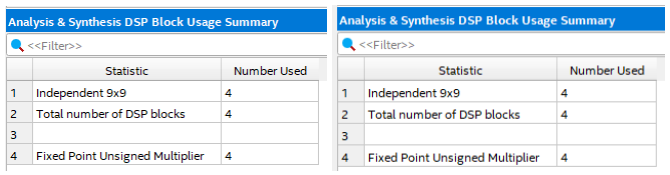
[picture p23: figure]

________________________________ איור 22 - צילומי מסך מ Quartus עבור Area של המערכת

### 7.2 Performance - תדר מקסימלי והנתיב הקריטי

.Fitter Seed = 2 | באמצעות | Quartus Prime 21.1ב־ Full Compilation עבר | הסופי | המימוש
עבור גרסת ה־MCU עם GPIO בלבד התקבל תדר מקסימלי של 21.9 MHz, בעוד עבור המימוש המלא התקבל MHz 20.73 = fmax. בשתי התצורות תדר העבודה שנבחר עבור MCLK הוא 20 MHz, ולכן שתי התצורות עומדות בתדר העבודה הנדרש. במימוש המלא נשאר מרווח של 0.73 MHz בין תדר העבודה לבין ה־fmax שהתקבל.

הנתיב הקריטי נמצא באזור ליבת ה־I32RV החד־מחזורית. בצילומי הנתיב הקריטי ניתן לראות מסלול ארוך העובר דרך מספר רב של רכיבי לוגיקה לאורך נתיב עיבוד הפקודה ומגיע לכיוון זיכרון הנתונים. מאחר שמדובר בארכיטקטורת Cycle-Single, הבאת הפקודה, הפענוח, בחירת האופרנדים, הביצוע וחישוב הגישה לזיכרון צריכים להסתיים כולם בתוך מחזור שעון יחיד. כתוצאה מכך מתקבל מסלול קומבינטורי ארוך, והוא שמגביל את תדר ה־MCLK המקסימלי.

Performance

| fmax | does it cause the critical path) | sysclk Critical path (what is the slowest submodule and why ) fMCLK (= f
MCU with GPIO | 21.9 MHz | עובר מזיכרון הפקודות ב־IFETCH אל זיכרון הנתונים DTCM. מאחר שהמעבד חד־מחזורי, שלבי הבאת הפקודה, הפענוח, הביצוע וחישוב הגישה לזיכרון חייבים להסתיים באותו מחזור שעון, ולכן נוצר מסלול קומבינטורי ארוך שמגביל את תדר ה־MCLK המקסימלי. | MHz 20 הרכיב האיטי ביותר הוא ליבת ה־I32RV. הנתיב הקריטי
MCU with GPIO and Interrupt Capability | 20.73 MHz | החד־מחזורית, ועובר בקירוב מ־ITCM/IFETCH לכיוון ה־DTCM. הסיבה שהוא קריטי היא שבמעבד Cycle-Single כל שלבי עיבוד הפקודה - הבאת הפקודה, פענוח, בחירת האופרנדים, ביצוע וחישוב הכתובת לזיכרון - חייבים להסתיים בתוך מחזור שעון אחד. לכן נוצר מסלול קומבינטורי ארוך שעובר דרך הרבה לוגיקה ו־MUXים, והוא זה שמגביל את תדר ה־MCLK המקסימלי. | MHz 20 המסלול הקריטי נמצא בתוך ליבת ה־I32RV

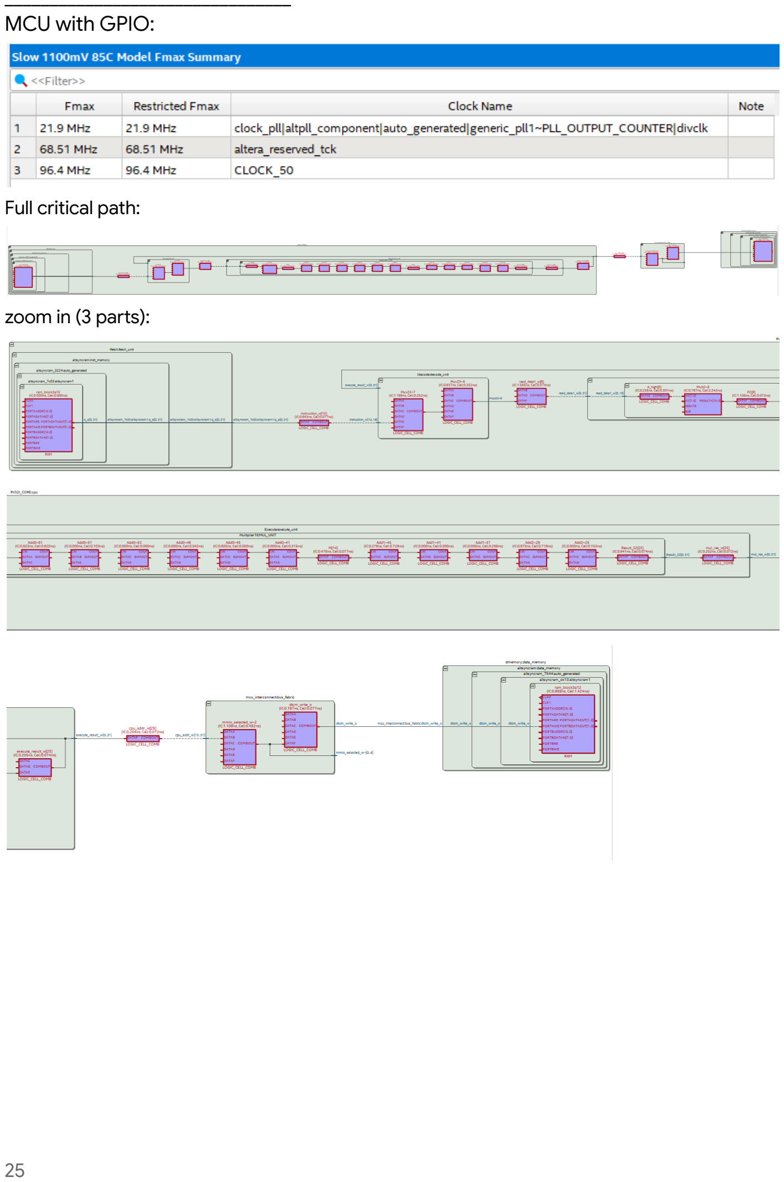
[picture p24: page 26]

________________________________ MCU with GPIO:

Full critical path:

zoom in (3 parts):

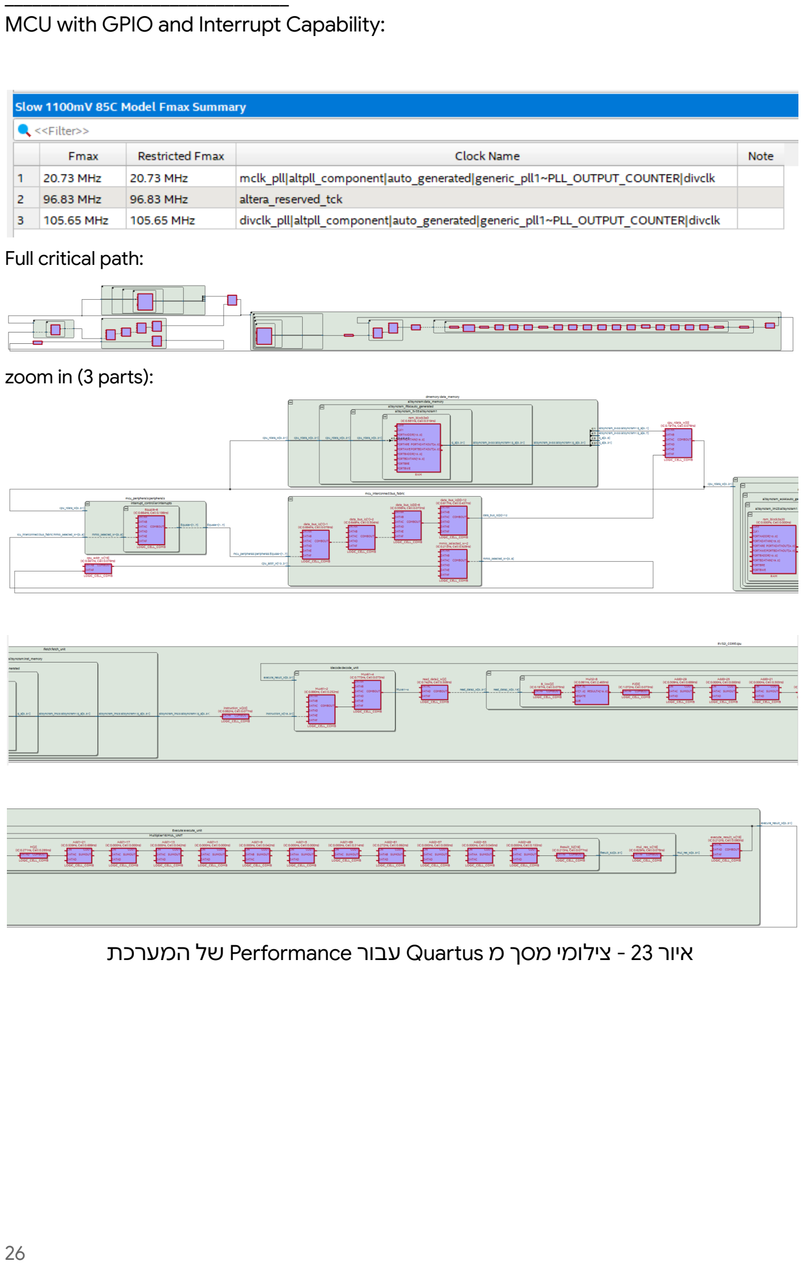
[picture p25: page 27]

_______________________________
MCU with GPIO and Interrupt Capability:

Full critical path:

zoom in (3 parts):

איור 23 - צילומי מסך מ Quartus עבור Performance של המערכת

### 7.3 Power - צריכת הספק

עבור גרסת ה־MCU עם GPIO בלבד התקבלה צריכת הספק כוללת של 461.52 mW, המורכבת מ־415.39 mW הספק סטטי, 31.07 mW הספק דינמי ו־15.05 mW עבור O/I. עבור המימוש המלא התקבלה צריכה כוללת של 456.13 mW, מתוכה 415.36 mW סטטי,
.I/O | עבור | mW 11.77ו־ | דינמי | mW 29.00

בשתי התצורות ניתן לראות כי עיקר צריכת ההספק היא סטטית, והיא כמעט זהה בין המימושים. ההבדל בצריכת ההספק הכוללת קטן יחסית - כ־5.39 mW - כאשר בדוח שהתקבל למימוש המלא הערך הכולל אף נמוך מעט מזה של גרסת ה־GPIO בלבד. מאחר ש־Quartus מציין בדוחות אלו Low :Confidence Estimation Power, יש להתייחס לערכי ההספק כאומדן התלוי גם בפעילות המיתוג ששימשה את ה־Analyzer Power, ולא להסיק מההפרש הקטן לבדו שמימוש אחד בהכרח חסכוני יותר מהשני.

Power

| Total power consumption | Static power consumption | Dynamic power consumption | I/O power consumption
MCU with GPIO | 461.52 mW | 415.39 mW | 31.07 mW | 15.05 mW
MCU with GPIO and Interrupt Capability | 456.13 mW | 415.36 mW | 29.00 mW | 11.77 mW

________________________________
MCU with GPIO:

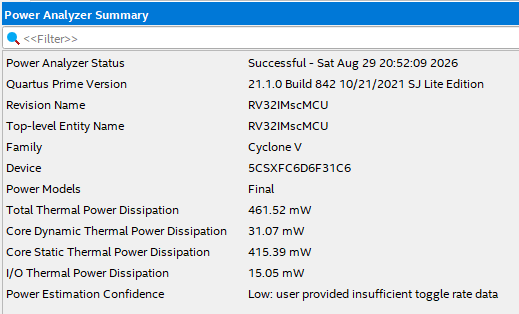
[picture p26: figure]

________________________________
MCU with GPIO and Interrupt Capability:

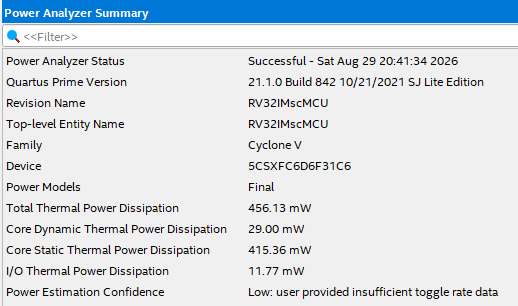
[picture p27: figure]

איור 24 - צילומי מסך מ Quartus עבור Power של המערכת

בסיכום אפיון ה־PPA, הוספת ה־Timer Basic, בקר הפסיקות ושאר הרכיבים בעלי יכולת הפסיקה הגדילה בעיקר את השימוש בלוגיקה וברגיסטרים והורידה במידה מסוימת את ה־fmax. עם זאת, המימוש המלא עדיין עומד בתדר העבודה הנדרש של 20 MHz, ללא שינוי בכמות הזיכרון המשובץ, במספר מכפלי ה־DSP או במספר ה־PLL-ים. צריכת ההספק הכוללת נשארה באותו סדר גודל בשתי התצורות.

## .8 מסקנות

בפרויקט תוכננה ומומשה מערכת MCU המבוססת על ליבת Cycle-Single IM32RV,
מערכת | ,Memory Mapped I/O | בשיטת | GPIO | ממשקי | ,DTCMו־ ITCM | זיכרונות | הכוללת
פסיקות, Timer Basic ומאיץ חלוקה רב־מחזורי עבור פעולות DIV ו־REM. במהלך העבודה בוצעה אינטגרציה בין כלל הרכיבים וכן התאמה בין מספר תחומי שעון באמצעות מנגנוני .CDC

תקינות המערכת נבדקה תחילה בסימולציות ModelSim באמצעות ארבע אפליקציות ה־Benchmark, ולאחר מכן נבדקה גם על גבי ה־FPGA באמצעות SignalTap. הבדיקות אימתו בין היתר את הטיפול בפסיקות KEY ובפסיקות ה־Timer Basic, את פעולת מאיץ החלוקה, את מצבי ה־Compare Output וה־Capture Input ואת יצירת אות ה־PWM במספר ערכי Cycle Duty. בכך התקבל אימות הן ברמת הסימולציה והן במימוש הפיזי של האינטגרציה בין ליבת המעבד והרכיבים הפריפריאליים.

מניתוח ה־PPA התקבל כי המימוש המלא משתמש ב־2074 Elements Logic וב־2007 רגיסטרים, ומגיע ל־MHz 20.73 = fmax. מאחר שתדר העבודה שנבחר עבור MCLK הוא 20 MHz, המימוש עומד בדרישת התזמון. הוספת הרכיבים בעלי יכולת הפסיקה הגדילה בעיקר את השימוש בלוגיקה וברגיסטרים והקטינה מעט את ה־fmax ביחס לגרסת ה־GPIO בלבד, אך ללא שינוי בכמות הזיכרון המשובץ, במספר בלוקי ה־DSP או במספר ה־PLL-ים. צריכת ההספק הכוללת של המימוש המלא הוערכה ב־456.13 mW.

בסיום הפרויקט התקבלה מערכת MCU מלאה העומדת בדרישות הפונקציונליות של הפרויקט ומדגימה שילוב בין ליבת מעבד, רכיבי O/I Mapped Memory, מנגנון פסיקות, טיימר ומאיץ חומרה במימוש יחיד על גבי FPGA.
