noamkorinperi/VHDL_LAB_final/מעבדה קודמת שלנו/Lab5/DOC/Report_lab5.docx.pdf

## LAB5 – preparation report

## RISC-V Single-Cycle and Pipelined cores architecture

## נועם קורין פרי – 208138586

## רועי אגושביץ - 322720665

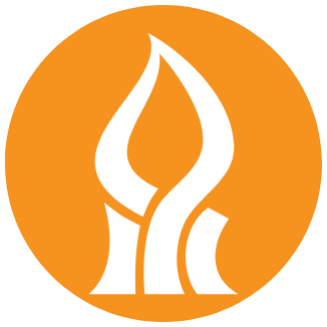
[picture p28: figure]

הקדמה:

מטרת מעבדה זו היא תכנון, סינתזה וניתוח של מעבד תואם V-RISC בארכיטקטורת Harvard, על גבי כרטיס FPGA-Intel. המעבדה נחלקת לשני חלקים מרכזיים. בחלק הראשון, הרחבנו ליבת I32RV cycle-single נתונה לארכיטקטורת MULDIV (IM32RV חלקי( על-ידי הוספת תמיכה בפקודת הכפל mul. פקודה זו כופלת את 16 הביטים התחתונים של רגיסטרי המקור )2rs 1,rs) ומחזירה תוצאה של 32 ביט ל-rd. המימוש מתבסס על חלוקת הפעולה לארבעה מכפלים של 8x8 ביט, לשם ניצול המכפלים המשובצים )Multipliers Embedded )של ה-FPGA, ללא שימוש במכפל כללי גדול.

בחלק השני, המרנו את הליבה המורחבת למעבד צינור )Pipeline )בעל חמישה שלבים: הבאת פקודה )IF), פענוח )ID), ביצוע )EX), גישה לזיכרון )MEM )וכתיבה חזרה )WB). לתמיכה בריבוי פקודות הרצות במקביל בצנרת והימנעות משגיאות תלות )Hazards Data), הוספנו יחידת Forwarding מלאה וכן מנגנון Stall( השהיה של מחזור יחיד( עבור מקרי use-load ו-use-mul. בנוסף, מומש מנגנון Flush לשטיפת פקודות שגויות מהצנרת במקרה של קפיצה מותנית )branch) שנלקחה או קפיצה בלתי מותנית )jump), אשר ההחלטה לגביהן מתקבלת בשלב הרביעי של הצינור. התכן פועל על שעון יחיד הנגזר מ-PLL, כאשר אות ה-Reset מחובר ללחצן 0KEY.

לצורך אפיון ביצועים ובדיקות על החומרה, הוספנו ל-level-Top מונים ייעודיים: מונה מחזורי שעון, מונה Stalls, מונה Flushes ורגיסטר לכתובת Breakpoint עבור יצירת טריגר ל-SignalTap. מהלך העבודה כלל אימות )Verification )ב-ModelSim מול מודל ייחוס של RARS( השוואת תוכן זיכרון ה-DTCM), חישוב ה-IPC, ואימות על החומרה )Validation )באמצעות SignalTap. לבסוף, ביצענו ניתוח PPA( ביצועים, שטח והספק( ב-Quartus להשוואה בין ליבת ה-Cycle-Single לליבת ה-Pipeline.

מקרה בדיקת ביצועים:

במקרה בדיקה זה נבדוק את הביצועים, השטח, צריכת ההספק והפונקציונליות של מערכת ספרתית.

סימולצית ModelSim:

נראה כמה מהסימולציות שלנו.

:Single-Cycle RV32IM ה עבור

באיור מוצגת סימולציית ModelSim עבור פקודת mul במעבד ה־IM32RV. ניתן לראות שבזמן שבו מזוהה פקודת כפל )1=detected_mul_tb), אותות הבקרה w_mul ו־w_op_mul פעילים. ערכי
תוצאת | ולכן | ,read_data2_o=0x00000008ו־ read_data1_o=0x00000001 הם | האופרנדים
הכפל הצפויה היא 00000008x.0 בפועל ניתן לראות שגם פלט המכפל o_Res, גם w_res_mul, וגם תוצאת ה־o_res_alu (ALU )שווים לערך זה. בנוסף, האות 1=match_mul_tb מאשר שה־testbench השווה בין התוצאה הצפויה לתוצאה שהמעבד הפיק ולא זיהה שגיאה.

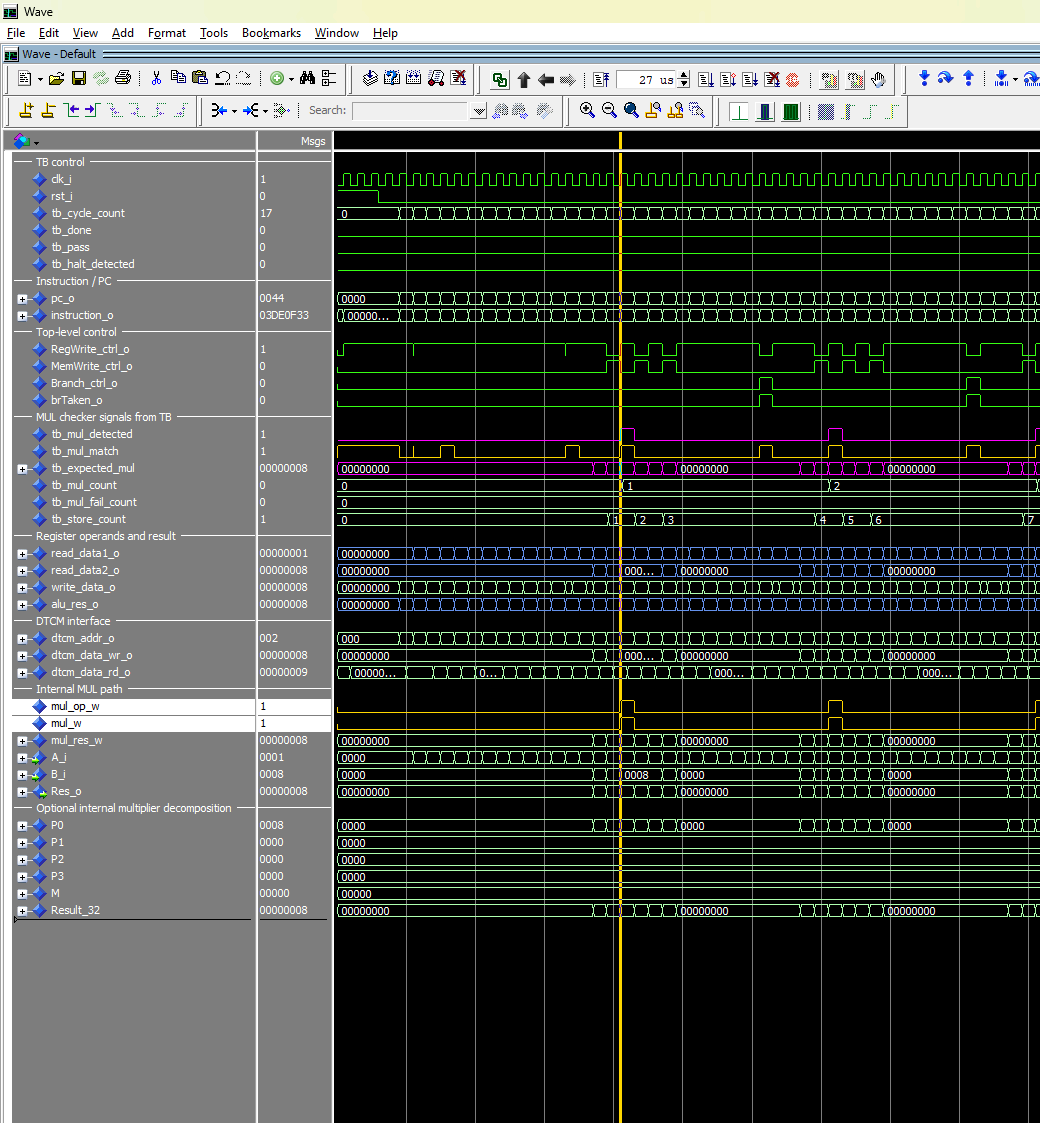
[picture p29: figure]

איור 1 – סימולצייה של ה IM32RV Cycle-Single ב ModelSim.

:Pipelined RV32IM ה עבור

בתמונה הראשונה מוצגת הרצת ModelSim של ליבת ה־IM32RV המצונרת. ניתן לראות את התקדמות ה־PC וה־instruction בין שלבי הצינור MEM ,EX ,ID ,IF, ו־WB. בנוסף מוצגים אותות הבקרה המרכזיים של המערכת, כולל מוני FHCNT/STCNT, מנגנוני flush ,stall, ו־forwarding, וכן פעילות בנתיב ה־MUL ובזיכרון הנתונים. התמונה משמשת כאימות כללי לכך שה־pipeline פעיל לאורך הריצה ושכל שלבי הצינור מתקדמים בצורה תקינה.

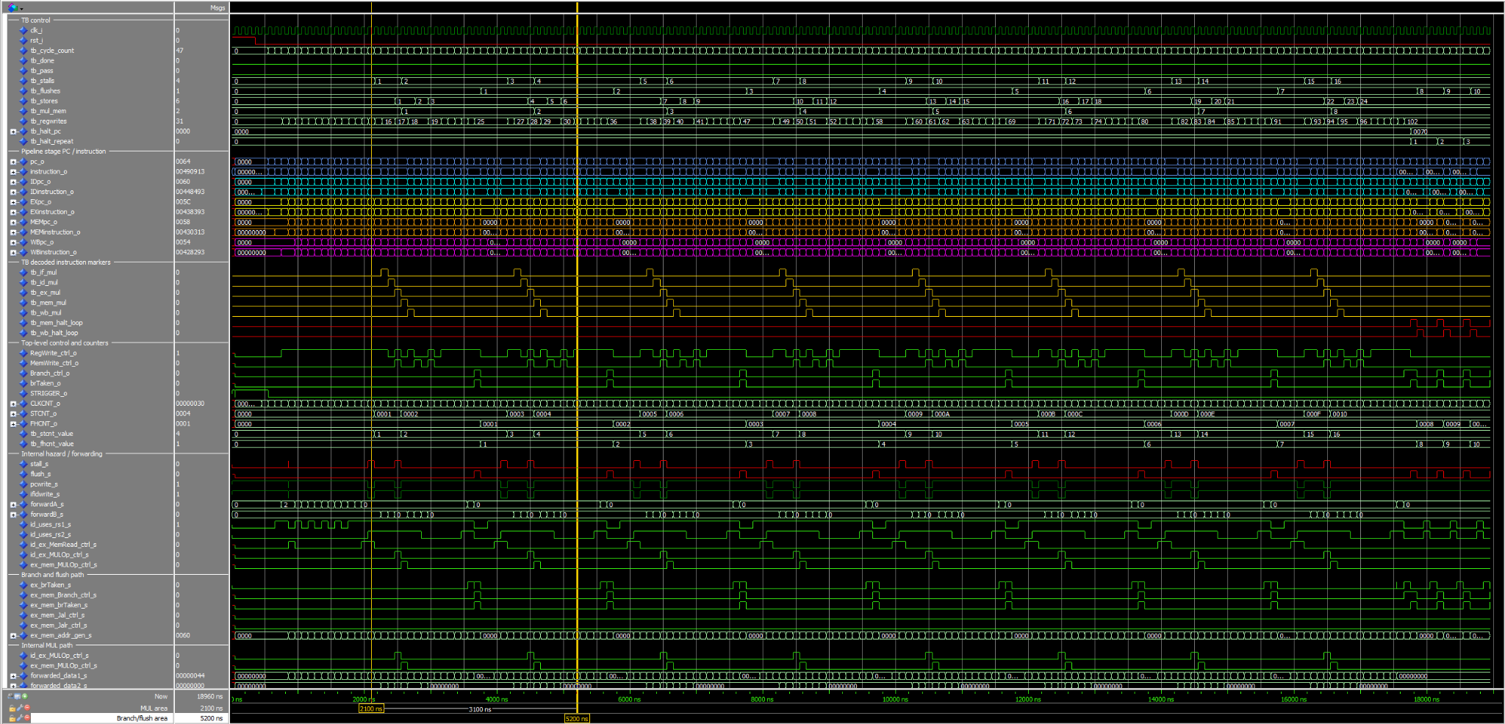
[picture p30: figure]

איור 2 – סימולצייה של ה IM32RV Pipelined ב ModelSim( רחב(.

בתמונה השנייה מוצג זום על אזור בהרצה שבו מופיעה פקודת mul ותלויות בין הוראות. ניתן לראות
tb_if_mul, tb_id_mul, tb_ex_mul, | הסמנים | בעזרת | הצינור | שלבי | בין | מתקדמת | שהפקודה
ובמקביל | ,עולה | stall_s | האות | ,hazard | מופיע | כאשר | , | בנוסף | .tb_wb_mulו־ ,tb_mem_mul
s_pcwrite ו־s_ifidwrite יורדים, כלומר ה־PC ורגיסטר ID/IF מוקפאים למחזור אחד. שינויי הערכים ב־s_forwardA ו־s_forwardB מראים שמנגנון ה־forwarding פעיל ומעביר ערכים מתאימים לשלב EX.

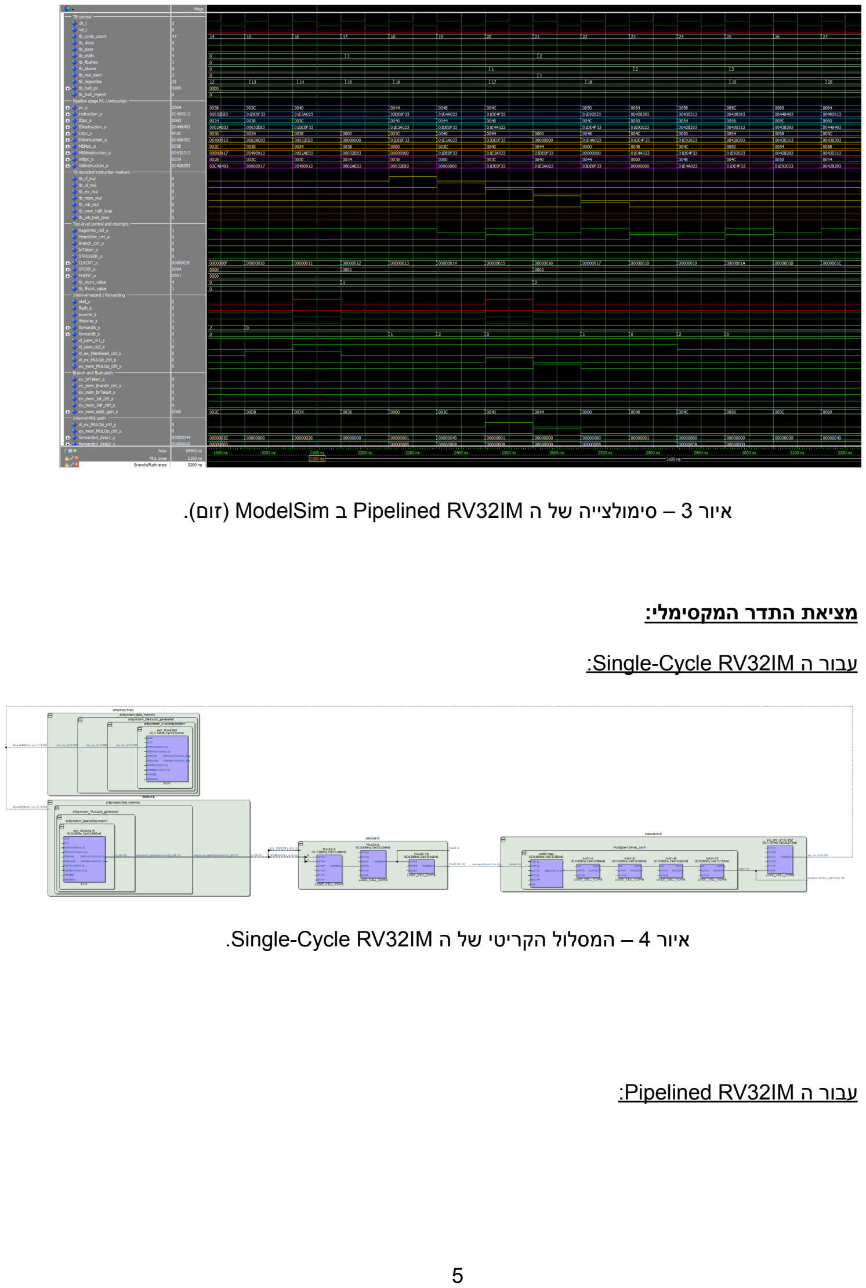
[picture p31: page 5]

איור 3 – סימולצייה של ה IM32RV Pipelined ב ModelSim( זום(.

מציאת התדר המקסימלי:

:Single-Cycle RV32IM ה עבור

איור 4 – המסלול הקריטי של ה IM32RV Cycle-Single.

:Pipelined RV32IM ה עבור

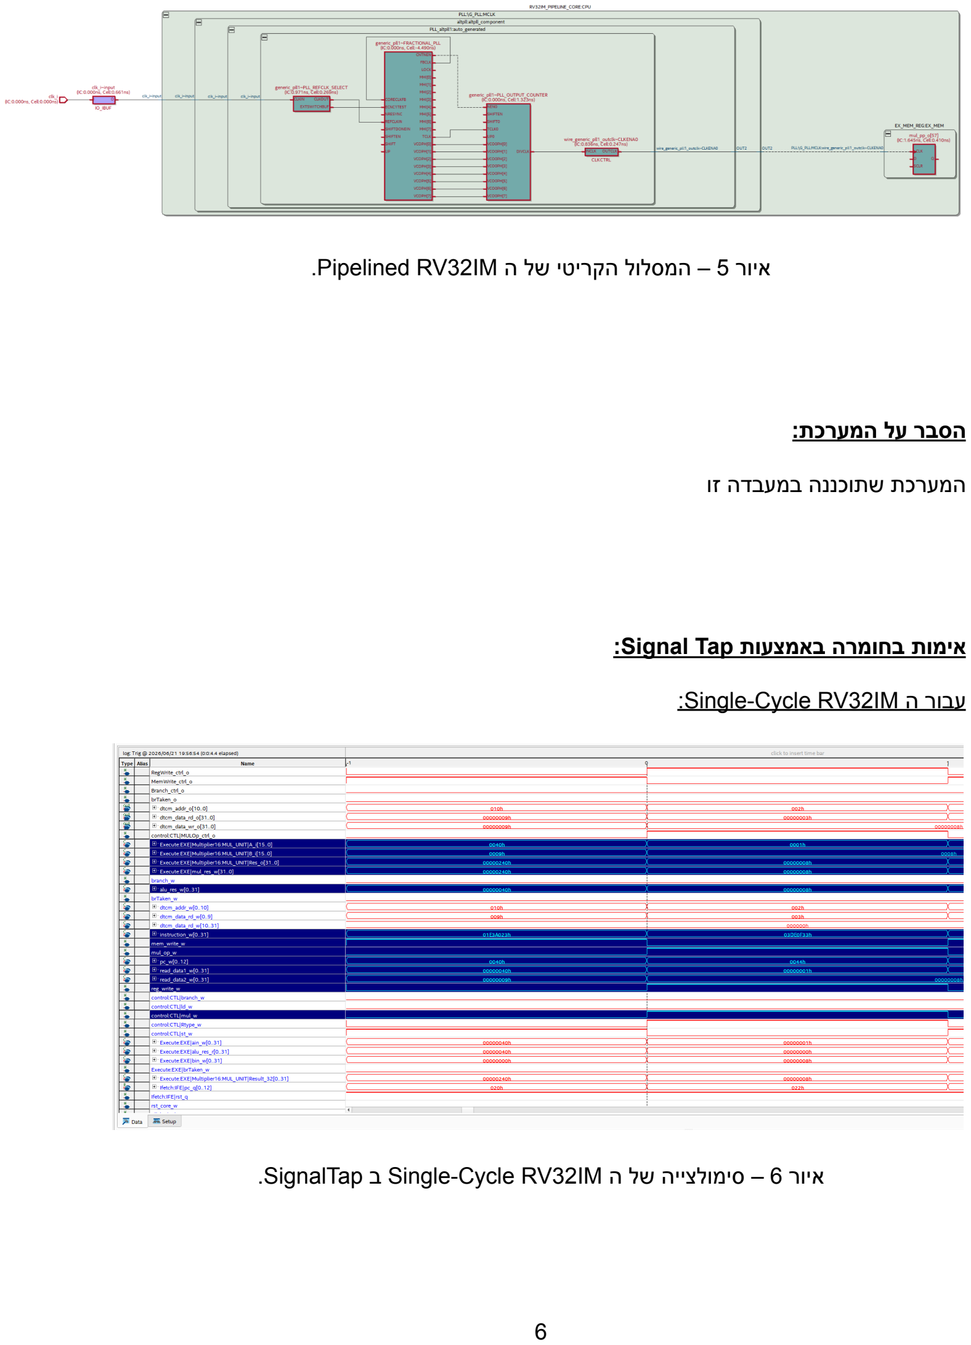
[picture p32: page 6]

איור 5 – המסלול הקריטי של ה IM32RV Pipelined.

הסבר על המערכת:

המערכת שתוכננה במעבדה זו

אימות בחומרה באמצעות Tap Signal:

:Single-Cycle RV32IM ה עבור

איור 6 – סימולצייה של ה IM32RV Cycle-Single ב SignalTap.

:Pipelined RV32IM ה עבור

בתמונה הראשונה ביצענו לכידה סביב כתובת שבה מופיעה פקודת mul. מטרת הבדיקה הייתה לוודא שהפקודה אכן עוברת בצורה תקינה בין שלבי הצינור. ניתן לראות את ה־PC וה־instruction מתקדמים בין שלבי MEM/EX ,EX/ID ,ID/IF ו־WB/MEM, ולכן מתקבלת אינדיקציה ברורה לפעולת ה־pipeline.

בנוסף, ניתן לראות ש־s_ctrl_MULOp_ex_id עולה כאשר פקודת ה־mul נמצאת בשלב EX, ולאחר מכן s_ctrl_MULOp_mem_ex עולה בשלב הבא. תוצאת הכפל מופיעה
דרך writebackה־ | לנתיב | מגיעה | ולבסוף | ,mem_wb_mul_res_sל־ | עוברת | ,mem_mul_res_sב־
s_data_write_wb. כך אומתה בפועל פעולת ה־path MUL בתוך הצינור.

באותה לכידה ניתן לראות גם התנהגות של handling hazard: כאשר יש תלות בין הוראות, s_stall עולה, ובמקביל s_pcwrite ו־s_ifidwrite יורדים. כלומר, ה־PC ו־ID/IF מוקפאים למחזור אחד, כפי שנדרש עבור use-load או hazard use-mul. בנוסף, ניתן לראות שינוי ב־s_forwardA ו־s_forwardB, דבר שמראה שמנגנון ה־forwarding פעיל.

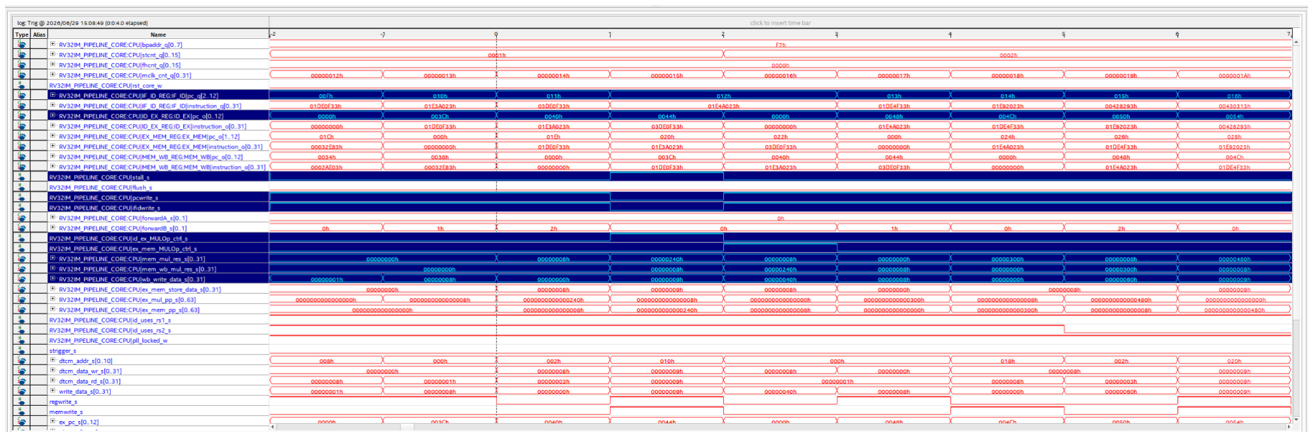
[picture p33: figure]

.)MUL and pipeline flow | עבור | )SignalTap ב Pipelined RV32IM ה של | סימולצייה | – 7 איור

בתמונה השנייה ביצענו לכידה סביב פקודת branch. מטרת הבדיקה הייתה לוודא ש־branch שנלקח גורם ל־flush נכון של ה־pipeline.

ניתן לראות שכאשר הפקודה מגיעה לשלב MEM/EX, האות s_ctrl_Branch_mem_ex פעיל, ובמקביל s_brTaken_mem_ex עולה. כלומר, מדובר בפקודת branch שהתנאי שלה התקיים. בעקבות זאת האות s_flush עולה, ומיד לאחר מכן מונה ה־flush, כלומר q_fhcnt, גדל מ־h0000 ל־h.0001

לכן התמונה מאשרת שמנגנון ה־hazard control עובד כראוי: כאשר branch נלקח בשלב הרביעי של הצינור, ההוראות השגויות שנכנסו ל־pipeline נשטפות, ומונה ה־flush מתעד את האירוע.

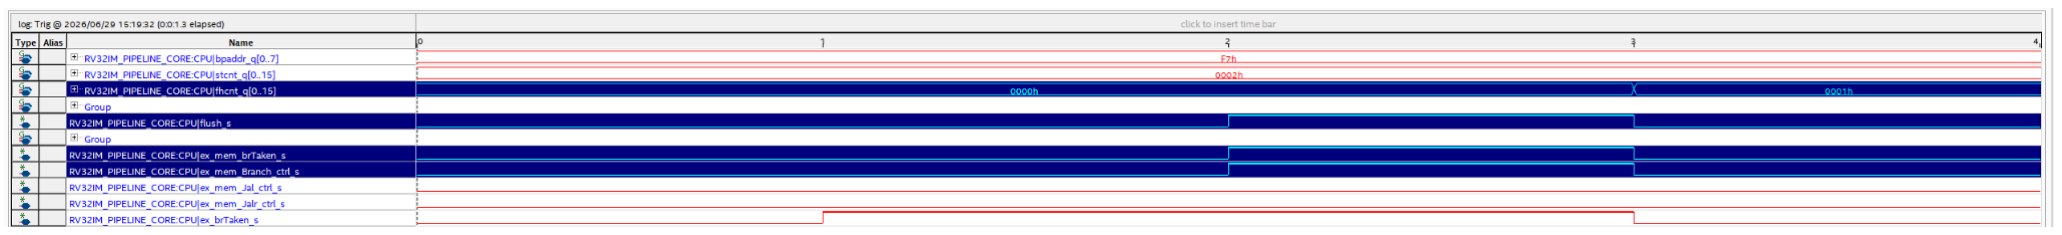
[picture p34: figure]

.)Branch and flush | עבור | )SignalTap ב Pipelined RV32IM ה של | סימולצייה | – 8 איור

אפיון ה-PPA( ביצועים, הספק, שטח( של המערכת הספרתית:

סיכום בטבלאות:

Area

| Logic elements | Registers | I/O pins | Embedded memory bits | Embedded 9-bit Multipliers | PLLs
Single-Cycle RV32IM | 1939 | 2519 | 270 | 401,408 | 4 fixed-point unsigned multipliers | 1
Pipelined RV32IM | 4527 | 11,047 | 265 | 3,084,288 | 4 fixed-point unsigned multipliers | 1
- print screens:

- Single-Cycle RV32IM:

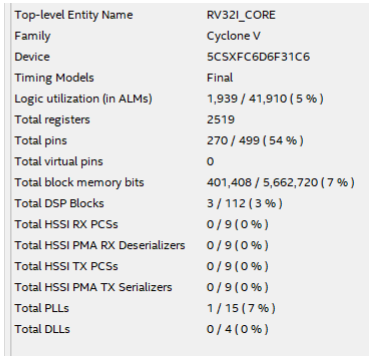
[picture p35: figure]

בנוסף ניתן לראות שימוש ב4 מכפלים באמצעות 3 BLOCKS DSP:

- Pipelined RV32IM:

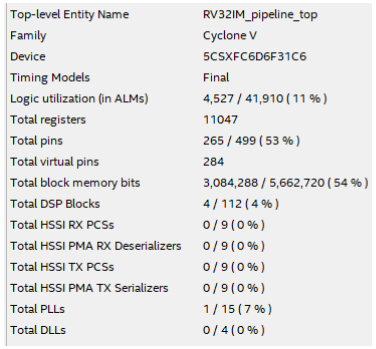
[picture p36: figure]

בנוסף ניתן לראות שימוש ב4 מכפלים

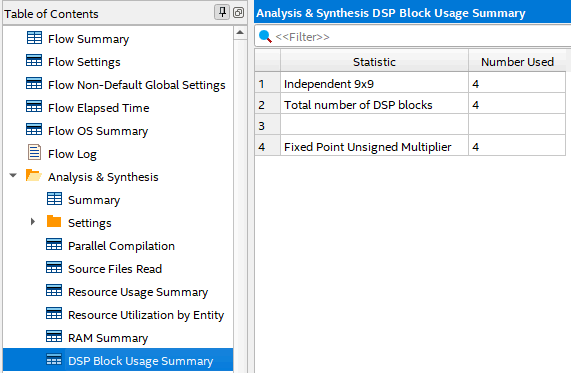
[picture p37: figure]

Performance

| fmax | Critical path (what is the slowest submodule and why does it cause the critical path) | ) fMCLK (= f sysclk
Single-Cycle RV32IM | 33.16 MHz | קומבינטורי ארוך של פקודה שלמה במחזור אחד, בעיקר דרך ה־Execute ונתיב ה־16Multiplier, יחד עם muxes מסביב. | MHz 25 המסלול הקריטי עובר דרך נתיב
Pipelined RV32IM | 114.26 MHz (~x3.5 factor) | שהנתיב הארוך חולק לשלבי pipeline. לפי צילום ה־path critical, המסלול המגביל נמצא סביב שעון ה־PLL / רגיסטר MEM_EX, ולא דרך נתיב פקודה מלא כמו ב־cycle-single. | MHz 100 המסלול הקריטי קצר יותר, משום
- print screens:
- Single-Cycle RV32IM:

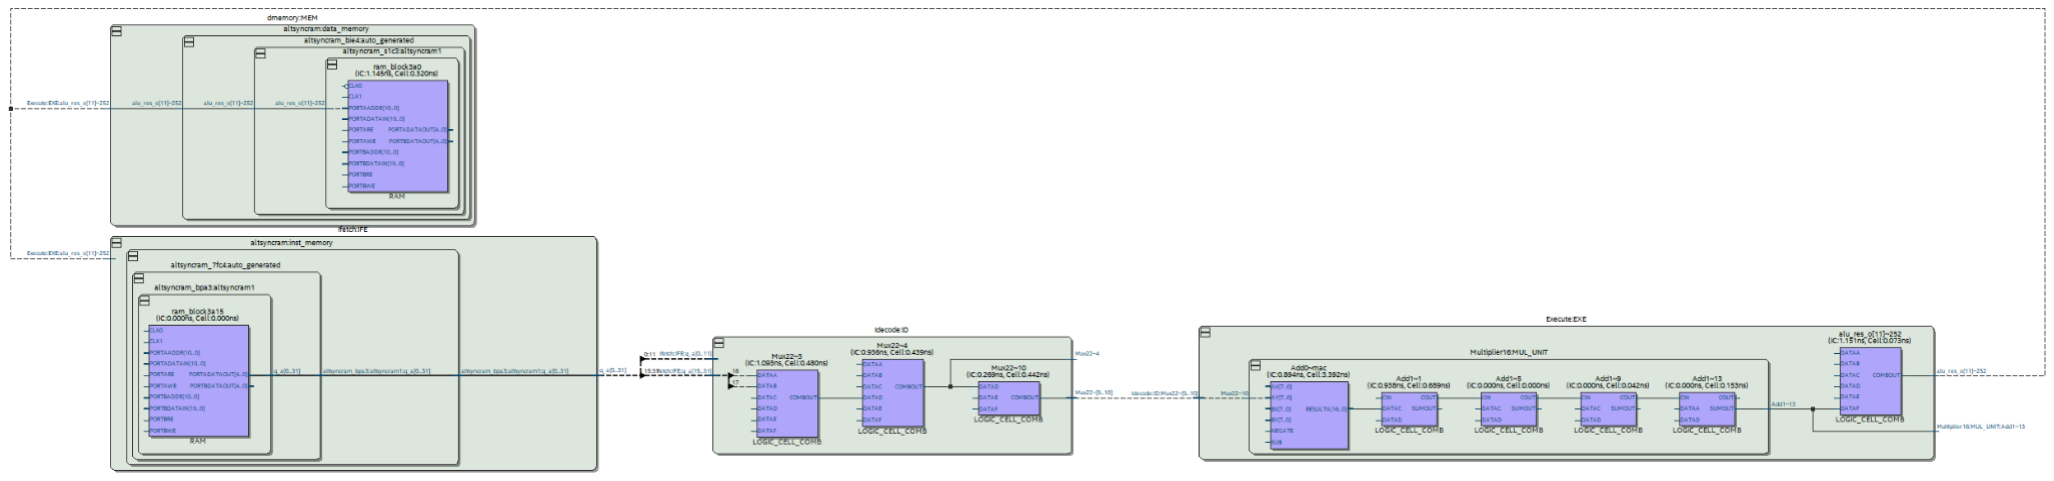
[picture p38: figure]

- Pipelined RV32IM:

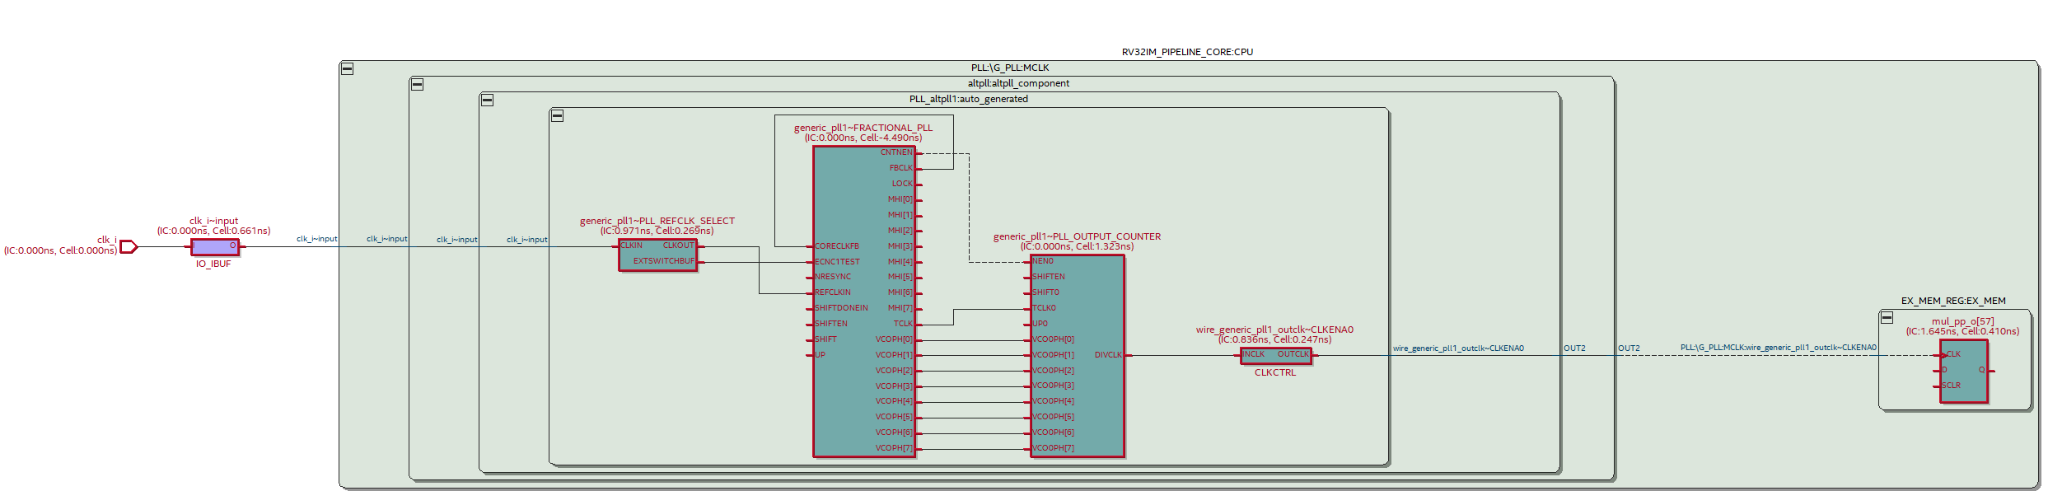
[picture p39: figure]

Power

| Total power consumption | Static power consumption | Dynamic power consumption | I/O power consumption
Single-Cycle RV32IM | 455.70 mW | 415.67 mW | 24.21 mW | 15.81 mW
Pipelined RV32IM | 570.57 mW | 419.55 mW | 119.93 mW | 31.09 mW
- print screens:

- Single-Cycle RV32IM:

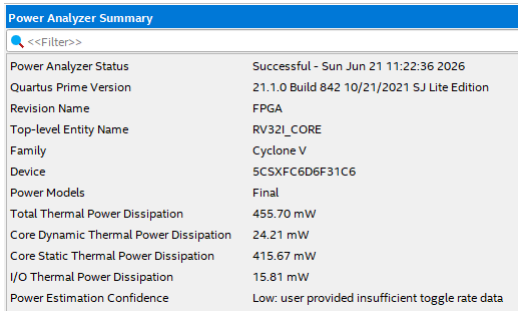
[picture p40: figure]

- Pipelined RV32IM:

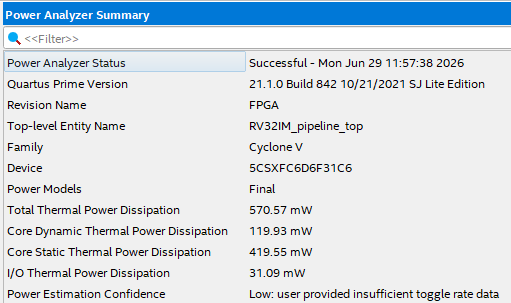
[picture p41: figure]

מסקנות:

מביצוע מעבדה זו וניתוח התוצאות, ניתן להסיק מספר מסקנות מרכזיות הנוגעות לפונקציונליות ולאפיון ה-PPA של המערכת:

.1 נכונות פונקציונלית ואימות בחומרה: שתי הליבות אומתו בהצלחה בסימולציית ModelSim מול מודל הייחוס RARS, והציגו התאמה מלאה בתוכן זיכרון ה-DTCM בסיום ריצת התוכניות. בנוסף, בדיקות ה-SignalTap על ה-FPGA אימתו את פעולת ה-Pipeline הלכה למעשה: ניתן לראות כי פקודת ה-mul מתקדמת כראוי בין שלבי הצינור )עליית MULOp בשלב EX והתקדמות עד נתיב ה-Writeback). במקרי תלות נתונים, נצפתה עליית האות
.)ifidwrite_s-ו pcwrite_s | האותות | ירידת | ) | כמצופה | IF/ID | ורגיסטר | PC-ה | והקפאת | stall_s
כמו כן, מנגנון ה-Flush תפקד כראוי בעת קפיצה )taken branch – )נצפתה עלייה באות s_flush ומונה ה-q_fhcnt (flushes )גדל מ0000- ל0001- בהתאם למחיקת הפקודות השגויות מהצנרת.
.2 שיפור משמעותי בביצועים )Performance): המעבר מארכיטקטורת Cycle-Single ל-Pipeline הביא לשיפור ניכר בתדר העבודה המקסימלי )Fmax). התדר עלה מ33.16-MHz ל114.26- MHz, המהווה שיפור של פי ~.3.45 שיפור זה תואם לציפייה התיאורטית של שיפור פי 3 עד ,4 ומדגים כיצד חלוקת המסלול הקריטי למספר שלבים קצרים מקטינה את זמן המחזור. הסיבה לכך שלא הושג שיפור אידיאלי של פי 5 נעוצה בכך שחמשת השלבים אינם מאוזנים לחלוטין, וזמן המחזור נקבע על ידי השלב האיטי ביותר. .3 מחיר השטח )off-Trade Area): העלייה בביצועים לוותה בגידול משמעותי בניצול משאבי הלוגיקה והשטח. מספר ה-ALMs (Elements Logic )גדל פי ~2.3 )מ1,939- ל4,527-(, וכמות הרגיסטרים גדלה פי ~4.4 )מ2,519- ל11,047-(. גידול זה נובע ברובו המוחלט
אשר | ,(IF/ID, ID/EX, EX/MEM, MEM/WB( | השלבים | בין | הצינור | רגיסטרי | מהוספת
נדרשים לשמור נתונים ואותות בקרה, וכן מהוספת יחידות ה-Forwarding וה-Stall. יחד עם זאת, מספר המכפלים המשובצים נותר זהה )4 יחידות( וכך גם כמות ה-PLL, בהתאם לדרישות התכן.
.4 מחיר ההספק )off-Trade Power): ההספק הכולל של המערכת עלה בכ,25.2%-מ455.70- mW בתצורת ה-Cycle-Single ל570.57- mW בתצורת ה-Pipeline. בחינה מעמיקה של הדוחות מראה כי ההספק הסטטי נותר כמעט זהה )~415.67 mW לעומת ~419.55 mW), אך ההספק הדינמי גדל פי 5 )מ24.21- mW ל119.93- mW). תופעה זו צפויה לחלוטין ונובעת מהעלייה הדרמטית במספר הרגיסטרים שמחליפים מצב בכל מחזור, ומקצב השעון המהיר יותר המאפיין את ארכיטקטורת הצינור.

לסיכום, ההשוואה בין המימושים ממחישה הלכה למעשה את פשרת ה,-Power (PPA Area ,Performance )הקלאסית בתכנון מעבדים. ה-Pipeline מאפשר תדר עבודה גבוה ותפוקה אפקטיבית משמעותית )גם לאחר התחשבות בירידת ה-IPC עקב stalls ו-flushes), אך השיפור מגיע במחיר בלתי נמנע של גידול בשטח המערכת, בכמות הלוגיקה, ובהספק הדינמי הנצרך. התוצאות מראות כי השיפור בביצועים )פי 3.45( מצדיק את התוספת בעלויות אלו עבור המערכת הנתונה.
