noamkorinperi/VHDL_LAB_final/SIM/RV32IMscMCU/screenshots/stage2_gpio_integration/stage2_gpio_integration.png

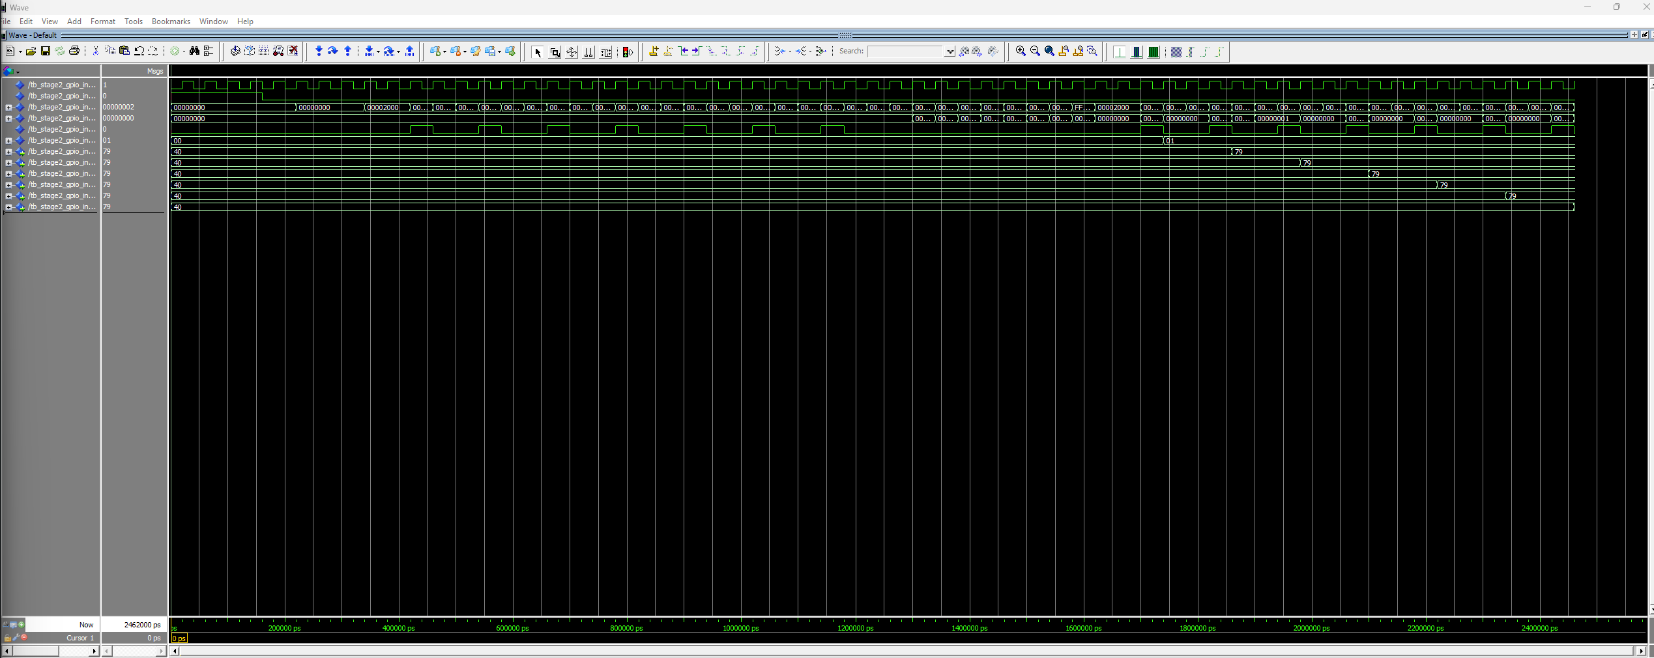
SIM/RV32IMscMCU/screenshots/stage2_gpio_integration/stage2_gpio_integration.png
