noamkorinperi/VHDL_LAB_final/SIM/RV32IMscMCU/screenshots/stage2_gpio_unit/stage 2.png

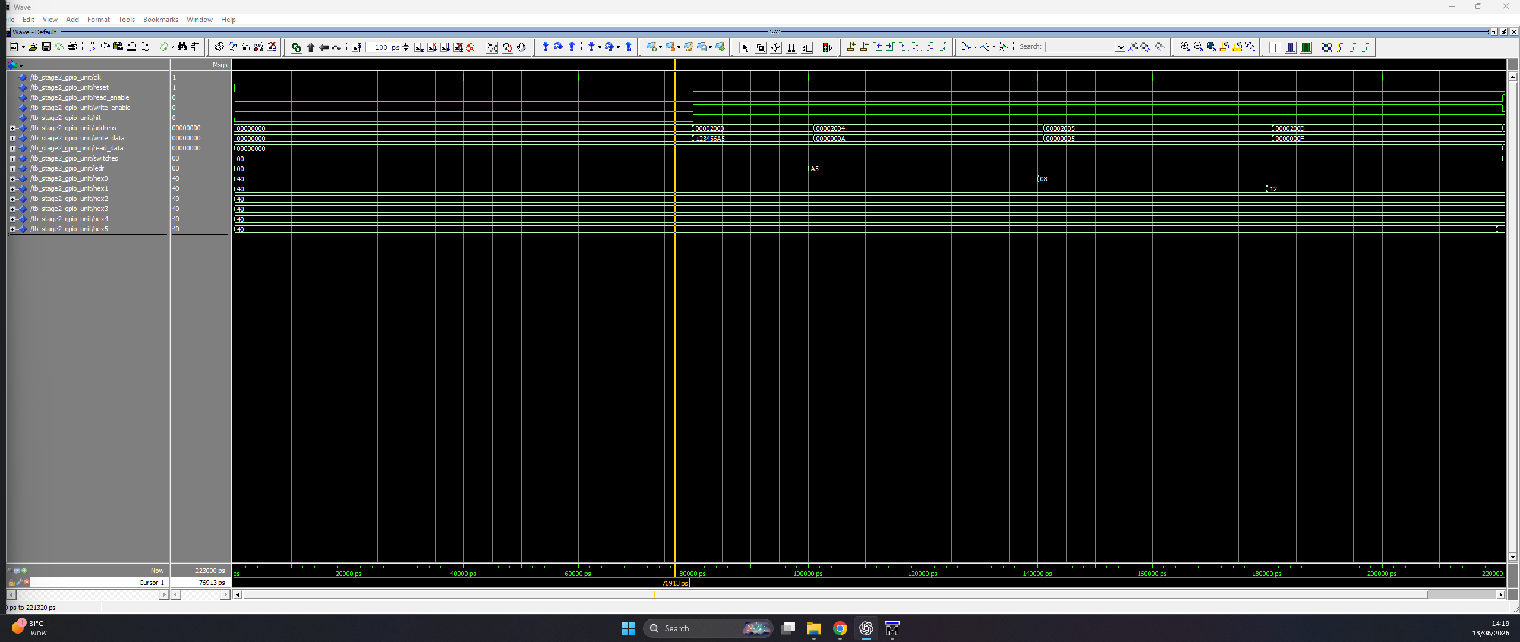
SIM/RV32IMscMCU/screenshots/stage2_gpio_unit/stage 2.png
