noamkorinperi/VHDL_LAB_final/SIM/RV32IMscMCU/screenshots/stage3_divider_unit/stage3_divider_unit.png

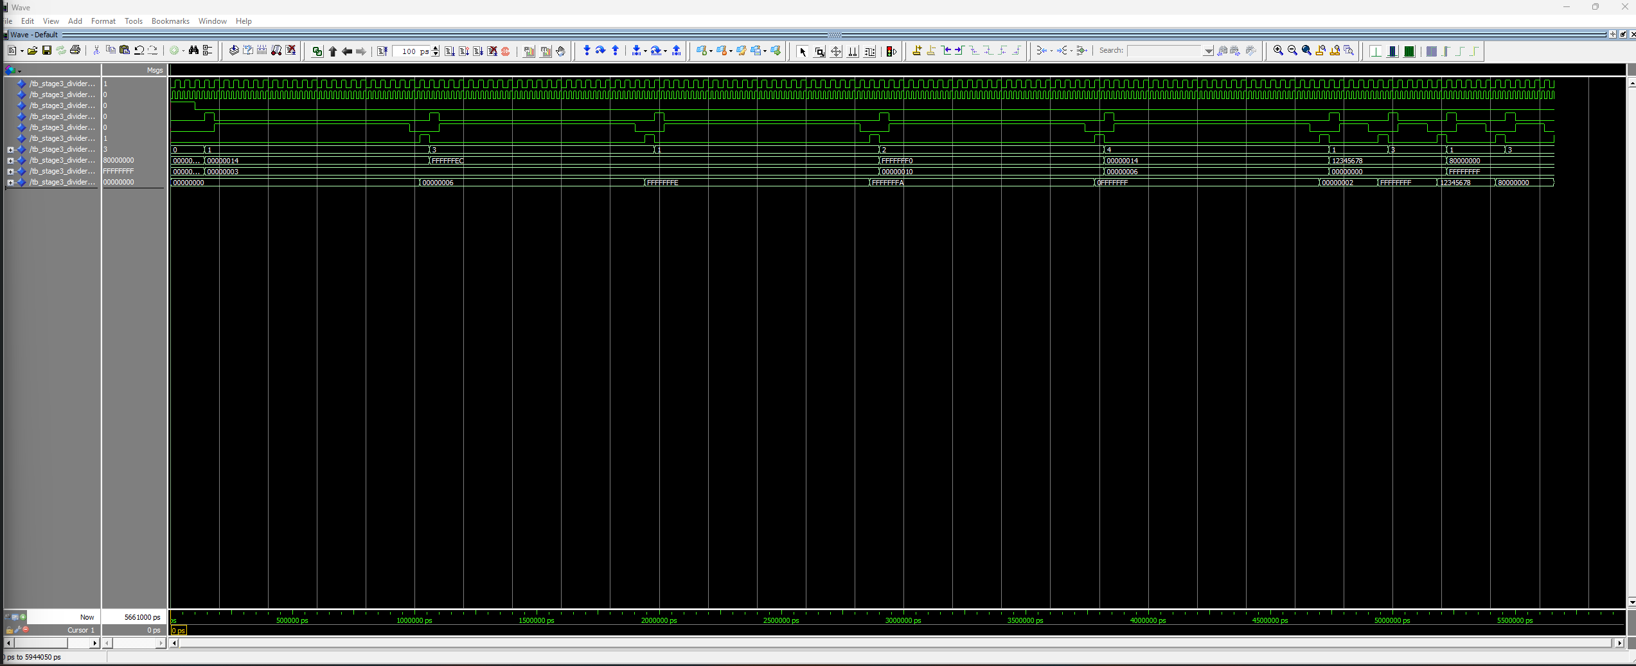
SIM/RV32IMscMCU/screenshots/stage3_divider_unit/stage3_divider_unit.png
