noamkorinperi/VHDL_LAB_final/SIM/RV32IMscMCU/screenshots/stage4_basic_timer/Screenshot 2026-08-17 221757.png

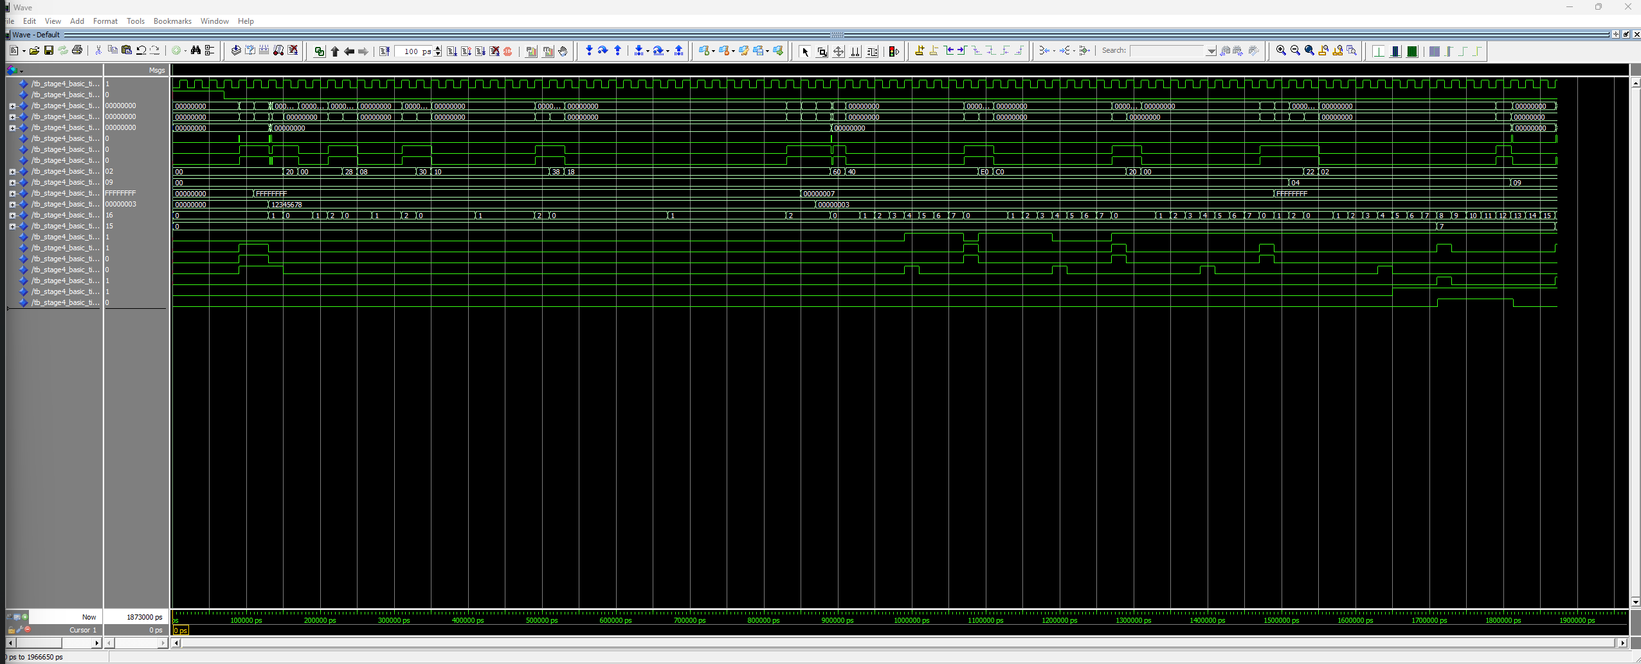
SIM/RV32IMscMCU/screenshots/stage4_basic_timer/Screenshot 2026-08-17 221757.png
