noamkorinperi/VHDL_LAB_final/SIM/RV32IMscMCU/screenshots/stage5_pushbuttons/Screenshot 2026-08-17 221931.png

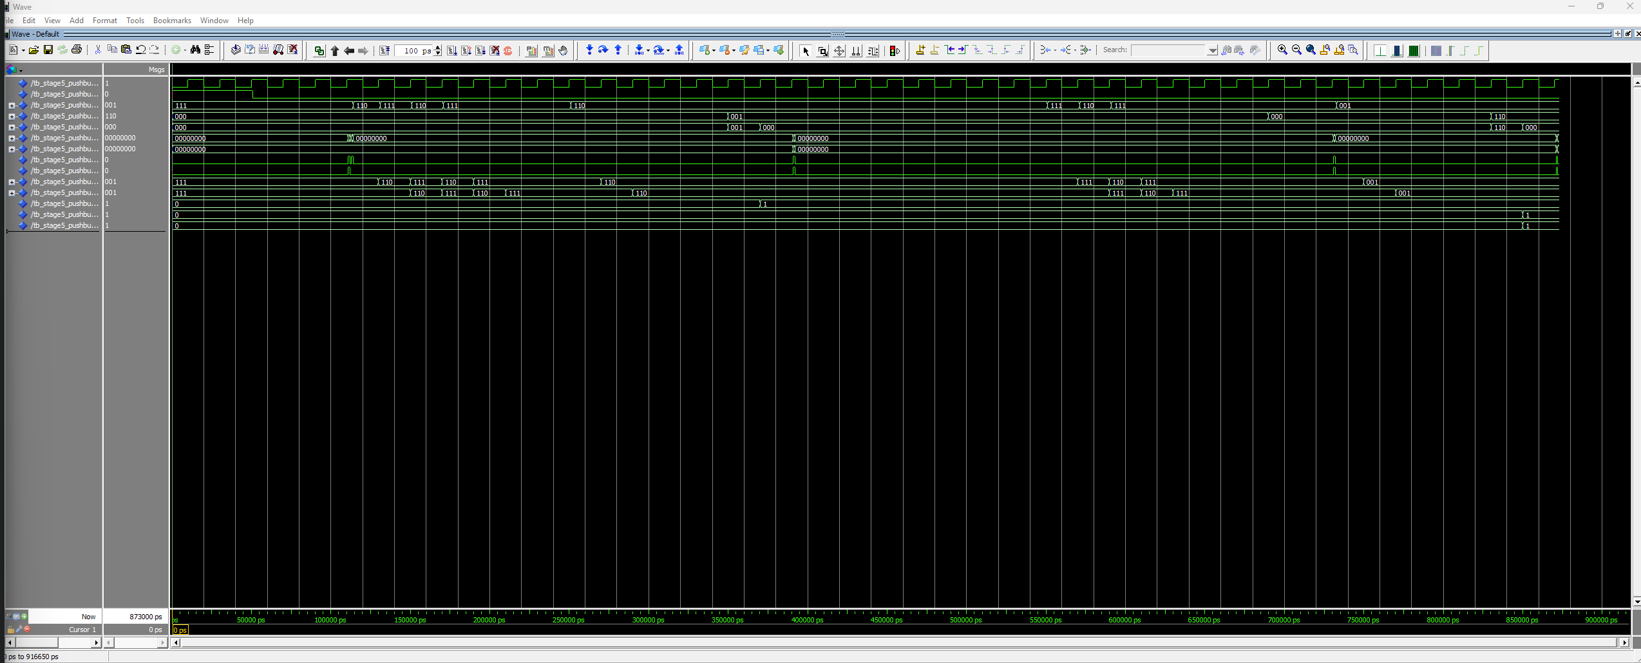
SIM/RV32IMscMCU/screenshots/stage5_pushbuttons/Screenshot 2026-08-17 221931.png
