noamkorinperi/VHDL_LAB_final/SIM/RV32IMscMCU/screenshots/stage 1/stage 1.png

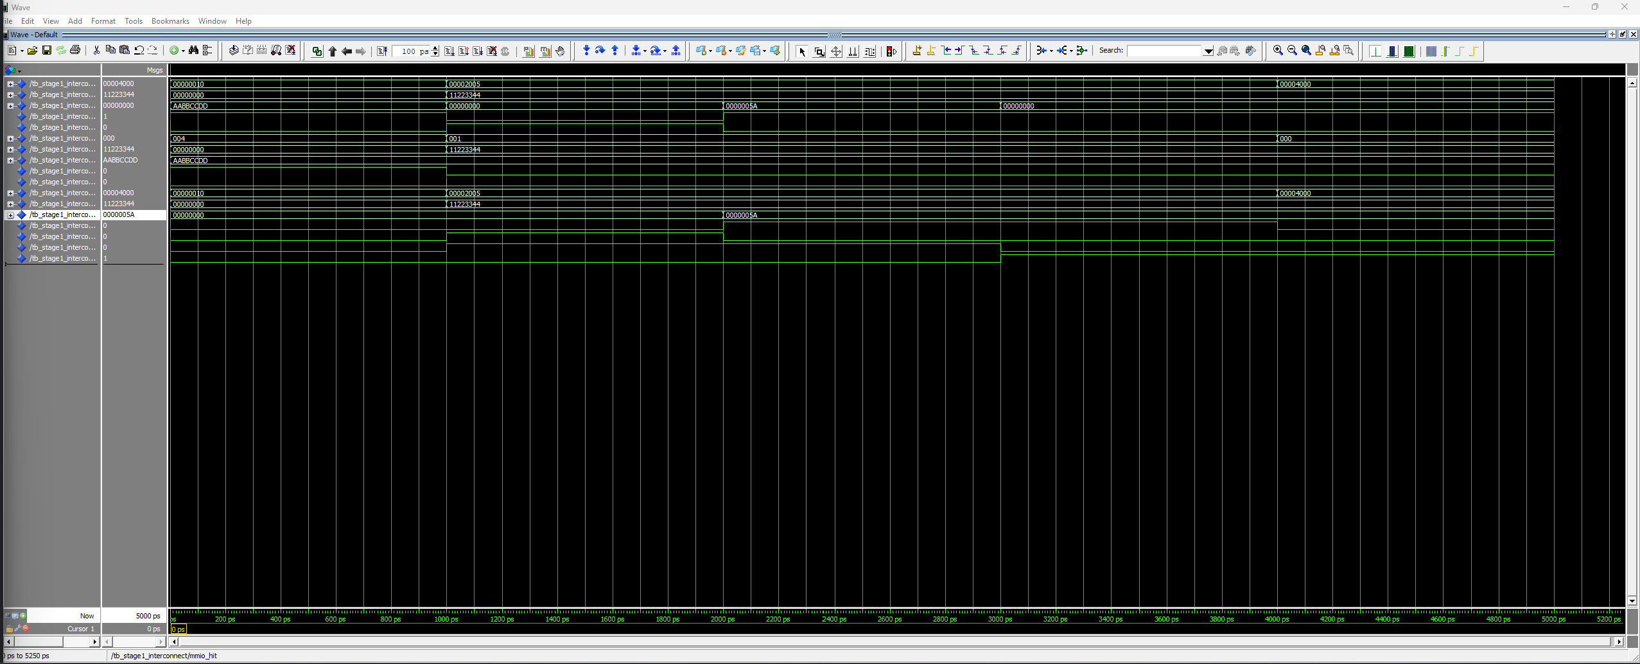
SIM/RV32IMscMCU/screenshots/stage 1/stage 1.png
