noamkorinperi/VHDL_LAB_final/SIM/RV32IMscMCU/screenshots/stage2_gpio_switch_benchmarks/stage2_gpio_switch_benchmarks.png

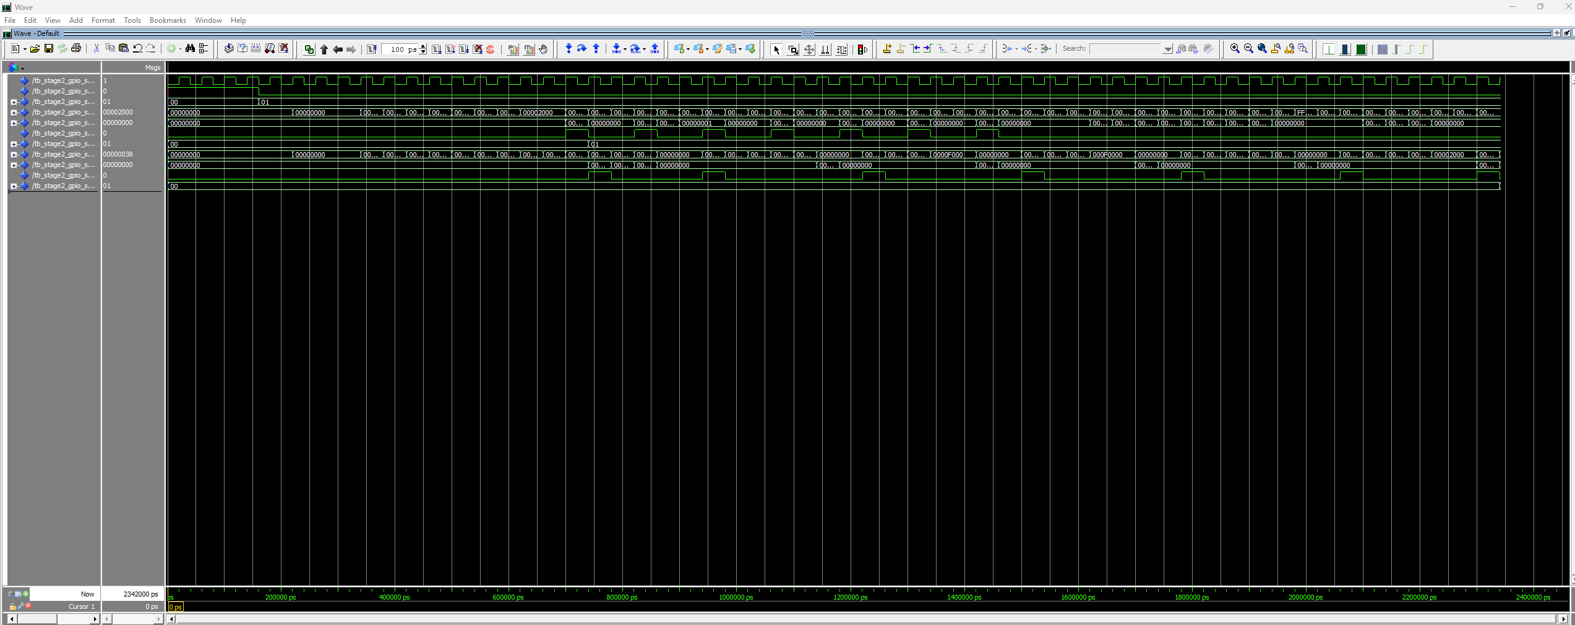
SIM/RV32IMscMCU/screenshots/stage2_gpio_switch_benchmarks/stage2_gpio_switch_benchmarks.png
